danjulio/gCore-featherwing/pictures/gcore_assy_1.png

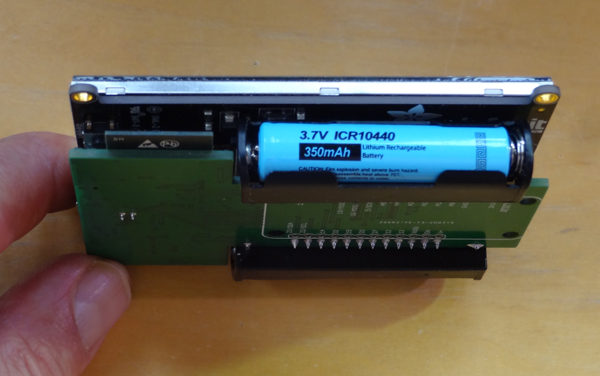
pictures/gcore_assy_1.png
