danjulio/gCore-featherwing/pictures/gcore_rev1_top.png

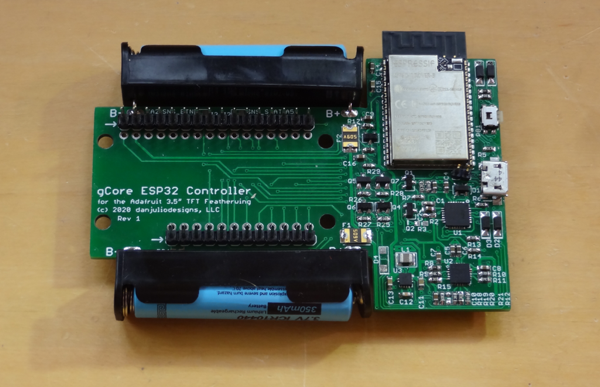
pictures/gcore_rev1_top.png
