danjulio/gCore-featherwing/pictures/gcore_side.png

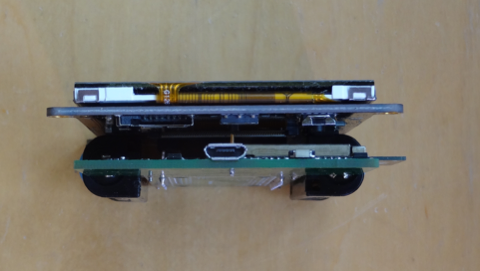
pictures/gcore_side.png
