danjulio/gCore-featherwing/software/LittlevGL/life/components/lvgl_esp32_drivers/lvgl_tft/disp_driver.c

/**
 * @file disp_driver.c
 */

#include "disp_driver.h"
#include "disp_spi.h"
#include "hx8357.h"


void disp_driver_init(bool init_spi)
{
	if (init_spi) {
		disp_spi_init();
	}
	
	hx8357_init(HX8357D);
}

void disp_driver_flush(lv_disp_drv_t * drv, const lv_area_t * area, lv_color_t * color_map)
{
	hx8357_flush(drv, area, color_map);
}
