danjulio/gCore-featherwing/software/FabGL/src/terminal.cpp

/*
  Created by Fabrizio Di Vittorio (fdivitto2013@gmail.com) - <http://www.fabgl.com>
  Copyright (c) 2019-2020 Fabrizio Di Vittorio.
  All rights reserved.

  This file is part of FabGL Library.

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
  You should have received a copy of the GNU General Public License
  along with FabGL.  If not, see <http://www.gnu.org/licenses/>.
 */


#include <stdarg.h>
#include <string.h>

#include "freertos/FreeRTOS.h"
#include "freertos/task.h"
#include "freertos/timers.h"

#include "rom/ets_sys.h"
#include "esp_attr.h"
#include "esp_intr.h"
#include "rom/uart.h"
#include "soc/uart_reg.h"
#include "soc/uart_struct.h"
#include "soc/io_mux_reg.h"
#include "soc/gpio_sig_map.h"
#include "soc/dport_reg.h"
#include "soc/rtc.h"
#include "esp_intr_alloc.h"


#include "fabutils.h"
#include "terminal.h"





namespace fabgl {


// Terminal identification ID
// 64 = VT420
// 1 = support for 132 columns
// 6 = selective erase
// 22 = color
const char TERMID[] = "?64;1;6;22c";

// to send 8 bit (S8C1T) or 7 bit control characters
const char CSI_7BIT[] = "\e[";
const char CSI_8BIT[] = "\x9B";
const char DCS_7BIT[] = "\eP";
const char DCS_8BIT[] = "\x90";
const char SS2_7BIT[] = "\eN";
const char SS2_8BIT[] = "\x8E";
const char SS3_7BIT[] = "\eO";
const char SS3_8BIT[] = "\x8F";
const char ST_7BIT[]  = "\e\\";
const char ST_8BIT[]  = "\x9C";
const char OSC_7BIT[] = "\e]";
const char OSC_8BIT[] = "\x9D";



#define ISCTRLCHAR(c) ((c) <= ASCII_US || (c) == ASCII_DEL)


// Map "DEC Special Graphics Character Set" to CP437
static const uint8_t DECGRAPH_TO_CP437[255] = {0, 1, 2, 3, 4, 5, 6, 7, 8, 9, 10, 11, 12, 13, 14, 15, 16, 17, 18, 19, 20, 21, 22, 23, 24, 25,
                                               26, 27, 28, 29, 30, 31, 32, 33, 34, 35, 36, 37, 38, 39, 40, 41, 42, 43, 44, 45, 46, 47, 48, 49,
                                               50, 51, 52, 53, 54, 55, 56, 57, 58, 59, 60, 61, 62, 63, 64, 65, 66, 67, 68, 69, 70, 71, 72, 73,
                                               74, 75, 76, 77, 78, 79, 80, 81, 82, 83, 84, 85, 86, 87, 88, 89, 90, 91, 92, 93, 94,
                                               /* 95 */ 32, /* 96 */ 4, /* 97 */ 177, /* 98 (not implemented) */ 63, /* 99 (not implemented) */ 63,
                                               /* 100 (not implemented) */ 63, /* 101 (not implemented) */ 63, /* 102 */ 248, /* 103 */ 241,
                                               /* 104 (not implemented) */ 63, /* 105 (not implemented) */ 63, /* 106 */ 217, /* 107 */ 191, /* 108 */ 218,
                                               /* 109 */ 192, /* 110 */ 197, /* 111 (not implemented) */ 63, /* 112 (not implemented) */ 63, /* 113 */ 196,
                                               /* 114 (not implemented) */ 63, /* 115 (not implemented) */ 63, /* 116 */ 195, /* 117 */ 180, /* 118 */ 193,
                                               /* 119 */ 194, /* 120 */ 179, /* 121 */ 243, /* 122 */ 242, /* 123 */ 227, /* 124 (not implemented) */ 63,
                                               /* 125 */ 156, /* 126 */ 249};


const char * CTRLCHAR_TO_STR[] = {"NUL", "SOH", "STX", "ETX", "EOT", "ENQ", "ACK", "BELL", "BS", "HT", "LF", "VT", "FF", "CR", "SO", "SI", "DLE", "XON", "DC2",
                                  "XOFF", "DC4", "NAK", "SYN", "ETB", "CAN", "EM", "SUB", "ESC", "FS", "GS", "RS", "US", "SPC"};



Terminal::Terminal()
  : m_canvas(nullptr)
{
}


Terminal::~Terminal()
{
  delete m_canvas;
}


void Terminal::begin(DisplayController * displayController, Keyboard * keyboard)
{
  m_displayController = displayController;

  m_canvas = new Canvas(m_displayController);

  m_keyboard = keyboard;
  if (m_keyboard == nullptr && PS2Controller::instance()) {
    // get default keyboard from PS/2 controller
    m_keyboard = PS2Controller::instance()->keyboard();
  }

  m_logStream = nullptr;

  m_glyphsBuffer = (GlyphsBuffer){0, 0, nullptr, 0, 0, nullptr};

  m_emuState.tabStop = nullptr;
  m_font.data = nullptr;

  set132ColumnMode(false);

  m_savedCursorStateList = nullptr;

  m_alternateScreenBuffer = false;
  m_alternateMap = nullptr;

  m_autoXONOFF = false;
  m_XOFF = false;

  // conformance level
  m_emuState.conformanceLevel = 4; // VT400
  m_emuState.ctrlBits = 7;

  // cursor setup
  m_cursorState   = false;
  m_emuState.cursorEnabled = false;

  m_mutex = xSemaphoreCreateMutex();

  // blink support
  m_blinkTimer = xTimerCreate("", pdMS_TO_TICKS(FABGLIB_DEFAULT_BLINK_PERIOD_MS), pdTRUE, this, blinkTimerFunc);
  xTimerStart(m_blinkTimer, portMAX_DELAY);

  // queue and task to consume input characters
  m_inputQueue = xQueueCreate(FABGLIB_TERMINAL_INPUT_QUEUE_SIZE, sizeof(uint8_t));
  xTaskCreate(&charsConsumerTask, "", FABGLIB_CHARS_CONSUMER_TASK_STACK_SIZE, this, FABGLIB_CHARS_CONSUMER_TASK_PRIORITY, &m_charsConsumerTaskHandle);

  m_defaultBackgroundColor = Color::Black;
  m_defaultForegroundColor = Color::White;

  m_serialPort = nullptr;
  m_keyboardReaderTaskHandle = nullptr;
  m_uart = false;

  m_outputQueue = nullptr;

  m_termInfo = nullptr;

  reset();
}


void Terminal::connectSerialPort(HardwareSerial & serialPort, bool autoXONXOFF)
{
  if (m_serialPort)
    vTaskDelete(m_keyboardReaderTaskHandle);
  m_serialPort = &serialPort;
  m_autoXONOFF = autoXONXOFF;

  m_serialPort->setRxBufferSize(FABGLIB_TERMINAL_INPUT_QUEUE_SIZE);

  if (m_keyboard->isKeyboardAvailable())
    xTaskCreate(&keyboardReaderTask, "", FABGLIB_KEYBOARD_READER_TASK_STACK_SIZE, this, FABGLIB_KEYBOARD_READER_TASK_PRIORITY, &m_keyboardReaderTaskHandle);

  // just in case a reset occurred after an XOFF
  if (m_autoXONOFF)
    send(ASCII_XON);
}


// returns number of bytes received (in the UART2 rx fifo buffer)
inline int uartGetRXFIFOCount()
{
  uart_dev_t * uart = (volatile uart_dev_t *)(DR_REG_UART2_BASE);
  return uart->status.rxfifo_cnt | ((int)(uart->mem_cnt_status.rx_cnt) << 8);
}


// flushes TX buffer of UART2
static void uartFlushTXFIFO()
{
  uart_dev_t * uart = (volatile uart_dev_t *)(DR_REG_UART2_BASE);
  while (uart->status.txfifo_cnt || uart->status.st_utx_out)
    ;
}


// flushes RX buffer of UART2
static void uartFlushRXFIFO()
{
  uart_dev_t * uart = (volatile uart_dev_t *)(DR_REG_UART2_BASE);
  while (uartGetRXFIFOCount() != 0 || uart->mem_rx_status.wr_addr != uart->mem_rx_status.rd_addr)
    uart->fifo.rw_byte;
}


// look into input queue (m_inputQueue): if there is space for new incoming bytes send XON and reenable uart RX interrupts
void Terminal::uartCheckInputQueueForFlowControl()
{
  if (m_autoXONOFF) {
    uart_dev_t * uart = (volatile uart_dev_t *)(DR_REG_UART2_BASE);
    if (uxQueueMessagesWaiting(m_inputQueue) == 0 && uart->int_ena.rxfifo_full == 0) {
      if (m_XOFF) {
        m_XOFF = false;
        uart->flow_conf.send_xon = 1; // send XON
      }
      uart->int_ena.rxfifo_full = 1;
    }
  }
}


// connect to UART2
void Terminal::connectSerialPort(uint32_t baud, uint32_t config, int rxPin, int txPin, FlowControl flowControl, bool inverted)
{
  Serial2.end();

  m_uart = true;
  m_autoXONOFF = (flowControl == FlowControl::Software);

  uart_dev_t * uart = (volatile uart_dev_t *)(DR_REG_UART2_BASE);

  DPORT_SET_PERI_REG_MASK(DPORT_PERIP_CLK_EN_REG, DPORT_UART2_CLK_EN);
  DPORT_CLEAR_PERI_REG_MASK(DPORT_PERIP_RST_EN_REG, DPORT_UART2_RST);

  // flush
  uartFlushTXFIFO();
  uartFlushRXFIFO();

  // set baud rate
  uint32_t clk_div = (getApbFrequency() << 4) / baud;
  uart->clk_div.div_int  = clk_div >> 4;
  uart->clk_div.div_frag = clk_div & 0xf;

  // frame
  uart->conf0.val = config;
  if (uart->conf0.stop_bit_num == 0x3) {
    uart->conf0.stop_bit_num = 1;
    uart->rs485_conf.dl1_en  = 1;
  }

  // RX Pin
  pinMode(rxPin, INPUT);
  pinMatrixInAttach(rxPin, U2RXD_IN_IDX, inverted);

  // RX interrupt
  uart->conf1.rxfifo_full_thrhd = 1;  // an interrupt for each character received
  uart->conf1.rx_tout_thrhd = 2;      // actually not used
  uart->conf1.rx_tout_en    = 0;      // timeout not enabled
  uart->int_ena.rxfifo_full = 1;      // interrupt on FIFO full (1 character - see rxfifo_full_thrhd)
  uart->int_ena.frm_err     = 1;      // interrupt on frame error
  uart->int_ena.rxfifo_tout = 0;      // no interrupt on rx timeout (see rx_tout_en and rx_tout_thrhd)
  uart->int_ena.parity_err  = 1;      // interrupt on rx parity error
  uart->int_ena.rxfifo_ovf  = 1;      // interrupt on rx overflow
  uart->int_clr.val = 0xffffffff;
  esp_intr_alloc(ETS_UART2_INTR_SOURCE, 0, uart_isr, this, nullptr);

  // setup FIFOs size
  uart->mem_conf.rx_size = 3;  // RX: 384 bytes (this is the max for UART2)
  uart->mem_conf.tx_size = 1;  // TX: 128 bytes

  // TX Pin
  pinMode(txPin, OUTPUT);
  pinMatrixOutAttach(txPin, U2TXD_OUT_IDX, inverted, false);

  // Flow Control
  uart->flow_conf.sw_flow_con_en = 0;
  uart->flow_conf.xonoff_del     = 0;
  if (flowControl == FlowControl::Software) {
    // we actually use manual software control, using send_xon/send_xoff bits to send control characters
    // because we have to check both RX-FIFO and input queue
    uart->swfc_conf.xon_threshold  = 0;
    uart->swfc_conf.xoff_threshold = 0;
    uart->swfc_conf.xon_char  = ASCII_XON;
    uart->swfc_conf.xoff_char = ASCII_XOFF;
    // send an XON right now
    m_XOFF = true;
    uart->flow_conf.send_xon = 1;
  }

  // APB Change callback (TODO?)
  //addApbChangeCallback(this, uart_on_apb_change);

  if (m_keyboard->isKeyboardAvailable())
    xTaskCreate(&keyboardReaderTask, "", FABGLIB_KEYBOARD_READER_TASK_STACK_SIZE, this, FABGLIB_KEYBOARD_READER_TASK_PRIORITY, &m_keyboardReaderTaskHandle);
}


void Terminal::connectLocally()
{
  m_outputQueue = xQueueCreate(FABGLIB_TERMINAL_OUTPUT_QUEUE_SIZE, sizeof(uint8_t));
  if (!m_keyboardReaderTaskHandle && m_keyboard->isKeyboardAvailable()) {
    xTaskCreate(&keyboardReaderTask, "", FABGLIB_KEYBOARD_READER_TASK_STACK_SIZE, this, FABGLIB_KEYBOARD_READER_TASK_PRIORITY, &m_keyboardReaderTaskHandle);
  }
}


void Terminal::logFmt(const char * format, ...)
{
  if (m_logStream) {
    va_list ap;
    va_start(ap, format);
    int size = vsnprintf(nullptr, 0, format, ap) + 1;
    if (size > 0) {
      char buf[size + 1];
      vsnprintf(buf, size, format, ap);
      m_logStream->write(buf);
    }
    va_end(ap);
  }
}


void Terminal::log(const char * txt)
{
  if (m_logStream)
    m_logStream->write(txt);
}


void Terminal::log(char c)
{
  if (m_logStream)
    m_logStream->write(c);
}


void Terminal::freeFont()
{
  #if FABGLIB_CACHE_FONT_IN_RAM
  if (m_font.data) {
    free((void*) m_font.data);
    m_font.data = nullptr;
  }
  #endif
}


void Terminal::freeTabStops()
{
  if (m_emuState.tabStop) {
    free(m_emuState.tabStop);
    m_emuState.tabStop = nullptr;
  }
}


void Terminal::freeGlyphsMap()
{
  if (m_glyphsBuffer.map) {
    free((void*) m_glyphsBuffer.map);
    m_glyphsBuffer.map = nullptr;
  }
  if (m_alternateMap) {
    free((void*) m_alternateMap);
    m_alternateMap = nullptr;
  }
}


void Terminal::end()
{
  vTaskDelete(m_keyboardReaderTaskHandle);

  xTimerDelete(m_blinkTimer, portMAX_DELAY);
  vSemaphoreDelete(m_mutex);

  clearSavedCursorStates();

  vTaskDelete(m_charsConsumerTaskHandle);
  vQueueDelete(m_inputQueue);

  vQueueDelete(m_outputQueue);

  freeFont();
  freeTabStops();
  freeGlyphsMap();
}


void Terminal::reset()
{
  #if FABGLIB_TERMINAL_DEBUG_REPORT_DESCS
  log("reset()\n");
  #endif

  xSemaphoreTake(m_mutex, portMAX_DELAY);
  m_resetRequested = false;

  m_emuState.originMode            = false;
  m_emuState.wraparound            = true;
  m_emuState.insertMode            = false;
  m_emuState.newLineMode           = false;
  m_emuState.smoothScroll          = false;
  m_emuState.keypadMode            = KeypadMode::Numeric;
  m_emuState.cursorKeysMode        = false;
  m_emuState.keyAutorepeat         = true;
  m_emuState.cursorBlinkingEnabled = true;
  m_emuState.cursorStyle           = 0;
  m_emuState.allow132ColumnMode    = false;
  m_emuState.reverseWraparoundMode = false;
  m_emuState.backarrowKeyMode      = false;
  m_emuState.ANSIMode              = true;
  m_emuState.VT52GraphicsMode      = false;
  m_emuState.allowFabGLSequences   = 0;
  m_emuState.characterSetIndex     = 0;  // Select G0
  for (int i = 0; i < 4; ++i)
    m_emuState.characterSet[i] = 1;     // G0, G1, G2 and G3 = USASCII

  m_lastPressedKey = VK_NONE;

  m_blinkingTextVisible = false;
  m_blinkingTextEnabled = true;

  m_cursorState = false;

  m_convMatchedCount = 0;
  m_convMatchedItem  = nullptr;

  // this also restore cursor at top-left
  setScrollingRegion(1, m_rows);

  resetTabStops();

  m_glyphOptions = (GlyphOptions) {{
    .fillBackground   = 1,
    .bold             = 0,
    .reduceLuminosity = 0,
    .italic           = 0,
    .invert           = 0,
    .blank            = 0,
    .underline        = 0,
    .doubleWidth      = 0,
    .userOpt1         = 0,    // blinking
    .userOpt2         = 0,    // 0 = erasable by DECSED or DECSEL,  1 = not erasable by DECSED or DECSEL
  }};
  m_canvas->setGlyphOptions(m_glyphOptions);

  m_paintOptions = PaintOptions();

  reverseVideo(false);

  int_setBackgroundColor(m_defaultBackgroundColor);
  int_setForegroundColor(m_defaultForegroundColor);

  clearSavedCursorStates();

  int_clear();

  xSemaphoreGive(m_mutex);
}


void Terminal::loadFont(FontInfo const * font)
{
  #if FABGLIB_TERMINAL_DEBUG_REPORT_DESCS
  log("loadFont()\n");
  #endif

  freeFont();

  m_font = *font;
#if FABGLIB_CACHE_FONT_IN_RAM
  int size = m_font.height * 256 * ((m_font.width + 7) / 8);
  m_font.data = (uint8_t const*) malloc(size);
  memcpy((void*)m_font.data, font->data, size);
#else
  m_font.data = font->data;
#endif

  m_columns = tmin(m_canvas->getWidth() / m_font.width, 132);
  m_rows    = tmin(m_canvas->getHeight() / m_font.height, 32);

  freeTabStops();
  m_emuState.tabStop = (uint8_t*) malloc(m_columns);
  resetTabStops();

  freeGlyphsMap();
  m_glyphsBuffer.glyphsWidth  = m_font.width;
  m_glyphsBuffer.glyphsHeight = m_font.height;
  m_glyphsBuffer.glyphsData   = m_font.data;
  m_glyphsBuffer.columns      = m_columns;
  m_glyphsBuffer.rows         = m_rows;
  m_glyphsBuffer.map          = (uint32_t*) heap_caps_malloc(sizeof(uint32_t) * m_columns * m_rows, MALLOC_CAP_32BIT);
  m_alternateMap = nullptr;
  m_alternateScreenBuffer = false;

  setScrollingRegion(1, m_rows);
}


void Terminal::flush(bool waitVSync)
{
  #if FABGLIB_TERMINAL_DEBUG_REPORT_DESCS
  log("flush()\n");
  #endif

  while (uxQueueMessagesWaiting(m_inputQueue) > 0)
    ;
  m_canvas->waitCompletion(waitVSync);
}


// false = setup for 80 columns mode
// true = setup for 132 columns mode
void Terminal::set132ColumnMode(bool value)
{
  #if FABGLIB_TERMINAL_DEBUG_REPORT_DESCS
  log("set132ColumnMode()\n");
  #endif

  loadFont(getPresetFontInfo(m_canvas->getWidth(), m_canvas->getHeight(), (value ? 132 : 80), 25));
}


void Terminal::setBackgroundColor(Color color, bool setAsDefault)
{
  if (setAsDefault)
    m_defaultBackgroundColor = color;
  Print::printf("\e[%dm", (int)color + (color < Color::BrightBlack ? 40 : 92));
}


void Terminal::int_setBackgroundColor(Color color)
{
  m_emuState.backgroundColor = color;
  m_canvas->setBrushColor(color);
}


void Terminal::setForegroundColor(Color color, bool setAsDefault)
{
  if (setAsDefault)
    m_defaultForegroundColor = color;
  Print::printf("\e[%dm", (int)color + (color < Color::BrightBlack ? 30 : 82));
}


void Terminal::int_setForegroundColor(Color color)
{
  m_emuState.foregroundColor = color;
  m_canvas->setPenColor(color);
}


void Terminal::reverseVideo(bool value)
{
  if (m_paintOptions.swapFGBG != value) {
    m_paintOptions.swapFGBG = value;
    m_canvas->setPaintOptions(m_paintOptions);

    m_canvas->swapRectangle(0, 0, m_canvas->getWidth() - 1, m_canvas->getHeight() - 1);
  }
}


void Terminal::clear(bool moveCursor)
{
  Print::write("\e[2J");
  if (moveCursor)
    Print::write("\e[1;1H");
}


void Terminal::int_clear()
{
  #if FABGLIB_TERMINAL_DEBUG_REPORT_DESCS
  log("int_clear()\n");
  #endif

  m_canvas->clear();
  clearMap(m_glyphsBuffer.map);
}


void Terminal::clearMap(uint32_t * map)
{
  uint32_t itemValue = GLYPHMAP_ITEM_MAKE(ASCII_SPC, m_emuState.backgroundColor, m_emuState.foregroundColor, m_glyphOptions);
  uint32_t * mapItemPtr = map;
  for (int row = 0; row < m_rows; ++row)
    for (int col = 0; col < m_columns; ++col, ++mapItemPtr)
      *mapItemPtr = itemValue;
}


// return True if scroll down required
bool Terminal::moveUp()
{
  #if FABGLIB_TERMINAL_DEBUG_REPORT_DESCS
  log("moveUp()\n");
  #endif

  if (m_emuState.cursorY == m_emuState.scrollingRegionTop)
    return true;
  setCursorPos(m_emuState.cursorX, m_emuState.cursorY - 1);
  return false;
}


// return True if scroll up required
bool Terminal::moveDown()
{
  #if FABGLIB_TERMINAL_DEBUG_REPORT_DESCS
  log("moveDown()\n");
  #endif

  if (m_emuState.cursorY == m_emuState.scrollingRegionDown)
    return true;
  setCursorPos(m_emuState.cursorX, m_emuState.cursorY + 1);
  return false;
}


// Move cursor at left or right, wrapping lines if necessary
void Terminal::move(int offset)
{
  int pos = m_emuState.cursorX - 1 + (m_emuState.cursorY - 1) * m_columns + offset;  // pos is zero based
  int newY = pos / m_columns + 1;
  int newX = pos % m_columns + 1;
  if (newY < m_emuState.scrollingRegionTop) {
    newX = 1;
    newY = m_emuState.scrollingRegionTop;
  }
  if (newY > m_emuState.scrollingRegionDown) {
    newX = m_columns;
    newY = m_emuState.scrollingRegionDown;
  }
  setCursorPos(newX, newY);
}


void Terminal::setCursorPos(int X, int Y)
{
  m_emuState.cursorX = tclamp(X, 1, (int)m_columns);
  m_emuState.cursorY = tclamp(Y, 1, (int)m_rows);
  m_emuState.cursorPastLastCol = false;

  #if FABGLIB_TERMINAL_DEBUG_REPORT_DESCSALL
  logFmt("setCursorPos(%d, %d) => set to (%d, %d)\n", X, Y, m_emuState.cursorX, m_emuState.cursorY);
  #endif
}


int Terminal::getAbsoluteRow(int Y)
{
  #if FABGLIB_TERMINAL_DEBUG_REPORT_DESCS
  logFmt("getAbsoluteRow(%d)\n", Y);
  #endif

  if (m_emuState.originMode) {
    Y += m_emuState.scrollingRegionTop - 1;
    Y = tclamp(Y, m_emuState.scrollingRegionTop, m_emuState.scrollingRegionDown);
  }
  return Y;
}


void Terminal::enableCursor(bool value)
{
  Print::write("\e[?25");
  Print::write(value ? "h" : "l");
}


bool Terminal::int_enableCursor(bool value)
{
  bool prev = m_emuState.cursorEnabled;
  if (m_emuState.cursorEnabled != value) {
    m_emuState.cursorEnabled = value;
    if (m_emuState.cursorEnabled) {
      if (uxQueueMessagesWaiting(m_inputQueue) == 0)
        blinkCursor();  // just to show the cursor immediately
    } else {
      if (m_cursorState)
        blinkCursor(); // make sure cursor is hidden
    }
  }
  return prev;
}


bool Terminal::enableBlinkingText(bool value)
{
  bool prev = m_blinkingTextEnabled;
  m_blinkingTextEnabled = value;
  return prev;
}


// callback for blink timer
void Terminal::blinkTimerFunc(TimerHandle_t xTimer)
{
  Terminal * term = (Terminal*) pvTimerGetTimerID(xTimer);

  if (xSemaphoreTake(term->m_mutex, 0) == pdTRUE) {

    // cursor blink
    if (term->m_emuState.cursorEnabled && term->m_emuState.cursorBlinkingEnabled)
      term->blinkCursor();

    // text blink
    if (term->m_blinkingTextEnabled)
      term->blinkText();

    xSemaphoreGive(term->m_mutex);

  }
}


void Terminal::blinkCursor()
{
  m_cursorState = !m_cursorState;
  int X = (m_emuState.cursorX - 1) * m_font.width;
  int Y = (m_emuState.cursorY - 1) * m_font.height;
  switch (m_emuState.cursorStyle) {
    case 0 ... 2:
      // block cursor
      m_canvas->swapRectangle(X, Y, X + m_font.width - 1, Y + m_font.height - 1);
      break;
    case 3 ... 4:
      // underline cursor
      m_canvas->swapRectangle(X, Y + m_font.height - 2, X + m_font.width - 1, Y + m_font.height - 1);
      break;
    case 5 ... 6:
      // bar cursor
      m_canvas->swapRectangle(X, Y, X + 1, Y + m_font.height - 1);
      break;
  }
}


void Terminal::blinkText()
{
  m_blinkingTextVisible = !m_blinkingTextVisible;
  bool keepEnabled = false;
  int rows = m_rows;
  int cols = m_columns;
  m_canvas->beginUpdate();
  for (int y = 0; y < rows; ++y) {
    uint32_t * itemPtr = m_glyphsBuffer.map + y * cols;
    for (int x = 0; x < cols; ++x, ++itemPtr) {
      // character to blink?
      GlyphOptions glyphOptions = glyphMapItem_getOptions(itemPtr);
      if (glyphOptions.userOpt1) {
        glyphOptions.blank = !m_blinkingTextVisible;
        glyphMapItem_setOptions(itemPtr, glyphOptions);
        refresh(x + 1, y + 1);
        keepEnabled = true;
      }
    }
    m_canvas->waitCompletion(false);
  }
  m_canvas->endUpdate();
  if (!keepEnabled)
    m_blinkingTextEnabled = false;
}


void Terminal::nextTabStop()
{
  int actualColumns = m_columns;

  // if double width for current line then consider half columns
  if (getGlyphOptionsAt(1, m_emuState.cursorY).doubleWidth)
    actualColumns /= 2;

  int x = m_emuState.cursorX;
  while (x < actualColumns) {
    ++x;
    if (m_emuState.tabStop[x - 1])
      break;
  }
  setCursorPos(x, m_emuState.cursorY);
}


// setup tab stops. One every 8.
void Terminal::resetTabStops()
{
  for (int i = 0; i < m_columns; ++i)
    m_emuState.tabStop[i] = (i > 0 && (i % 8) == 0 ? 1 : 0);
}


// if column = 0 then clear all tab stops
void Terminal::setTabStop(int column, bool set)
{
  #if FABGLIB_TERMINAL_DEBUG_REPORT_DESCS
  logFmt("setTabStop %d %d\n", column, (int)set);
  #endif

  if (column == 0)
    memset(m_emuState.tabStop, 0, m_columns);
  else
    m_emuState.tabStop[column - 1] = set ? 1 : 0;
}


void Terminal::scrollDown()
{
  #if FABGLIB_TERMINAL_DEBUG_REPORT_DESCS
  log("scrollDown\n");
  #endif

  // scroll down using canvas
  if (m_emuState.smoothScroll) {
    for (int i = 0; i < m_font.height; ++i)
      m_canvas->scroll(0, 1);
  } else
    m_canvas->scroll(0, m_font.height);

  // move down scren buffer
  for (int y = m_emuState.scrollingRegionDown - 1; y > m_emuState.scrollingRegionTop - 1; --y)
    memcpy(m_glyphsBuffer.map + y * m_columns, m_glyphsBuffer.map + (y - 1) * m_columns, m_columns * sizeof(uint32_t));

  // insert a blank line in the screen buffer
  uint32_t itemValue = GLYPHMAP_ITEM_MAKE(ASCII_SPC, m_emuState.backgroundColor, m_emuState.foregroundColor, m_glyphOptions);
  uint32_t * itemPtr = m_glyphsBuffer.map + (m_emuState.scrollingRegionTop - 1) * m_columns;
  for (int x = 0; x < m_columns; ++x, ++itemPtr)
    *itemPtr = itemValue;

}


// startingRow: represents an absolute value, not related to the scrolling region
void Terminal::scrollDownAt(int startingRow)
{
  int prevScrollingRegionTop = m_emuState.scrollingRegionTop;
  setScrollingRegion(startingRow, m_emuState.scrollingRegionDown, false);

  scrollDown();

  setScrollingRegion(prevScrollingRegionTop, m_emuState.scrollingRegionDown, false);
}


void Terminal::scrollUp()
{
  #if FABGLIB_TERMINAL_DEBUG_REPORT_DESCS
  log("scrollUp\n");
  #endif

  // scroll up using canvas
  if (m_emuState.smoothScroll) {
    for (int i = 0; i < m_font.height; ++i)
      m_canvas->scroll(0, -1);
  } else
    m_canvas->scroll(0, -m_font.height);

  // move up screen buffer
  for (int y = m_emuState.scrollingRegionTop - 1; y < m_emuState.scrollingRegionDown - 1; ++y)
    memcpy(m_glyphsBuffer.map + y * m_columns, m_glyphsBuffer.map + (y + 1) * m_columns, m_columns * sizeof(uint32_t));

  // insert a blank line in the screen buffer
  uint32_t itemValue = GLYPHMAP_ITEM_MAKE(ASCII_SPC, m_emuState.backgroundColor, m_emuState.foregroundColor, m_glyphOptions);
  uint32_t * itemPtr = m_glyphsBuffer.map + (m_emuState.scrollingRegionDown - 1) * m_columns;
  for (int x = 0; x < m_columns; ++x, ++itemPtr)
    *itemPtr = itemValue;
}


void Terminal::scrollUpAt(int startingRow)
{
  int prevScrollingRegionTop = m_emuState.scrollingRegionTop;
  setScrollingRegion(startingRow, m_emuState.scrollingRegionDown, false);

  scrollUp();

  setScrollingRegion(prevScrollingRegionTop, m_emuState.scrollingRegionDown, false);
}


void Terminal::setScrollingRegion(int top, int down, bool resetCursorPos)
{
  m_emuState.scrollingRegionTop  = tclamp(top, 1, (int)m_rows);
  m_emuState.scrollingRegionDown = tclamp(down, 1, (int)m_rows);
  updateCanvasScrollingRegion();

  if (resetCursorPos)
    setCursorPos(1, m_emuState.originMode ? m_emuState.scrollingRegionTop : 1);

  #if FABGLIB_TERMINAL_DEBUG_REPORT_DESCS
  logFmt("setScrollingRegion: %d %d => %d %d\n", top, down, m_emuState.scrollingRegionTop, m_emuState.scrollingRegionDown);
  #endif
}


void Terminal::updateCanvasScrollingRegion()
{
  m_canvas->setScrollingRegion(0, (m_emuState.scrollingRegionTop - 1) * m_font.height, m_canvas->getWidth() - 1, m_emuState.scrollingRegionDown * m_font.height - 1);
}


// Insert a blank space at current position, moving next "charsToMove" characters to the right (even on multiple lines).
// Characters after "charsToMove" length are overwritter.
// Vertical scroll may occurs (in this case returns "True")
bool Terminal::multilineInsertChar(int charsToMove)
{
  bool scrolled = false;
  int col = m_emuState.cursorX;
  int row = m_emuState.cursorY;
  if (m_emuState.cursorPastLastCol) {
    ++row;
    col = 1;
  }
  uint32_t lastColItem = 0;
  while (charsToMove > 0) {
    uint32_t * rowPtr = m_glyphsBuffer.map + (row - 1) * m_columns;
    uint32_t lItem = rowPtr[m_columns - 1];
    insertAt(col, row, 1);
    if (row > m_emuState.cursorY) {
      rowPtr[0] = lastColItem;
      refresh(1, row);
    }
    lastColItem = lItem;
    charsToMove -= m_columns - col;
    col = 1;
    if (charsToMove > 0 && row == m_emuState.scrollingRegionDown) {
      scrolled = true;
      scrollUp();
      setCursorPos(m_emuState.cursorX, m_emuState.cursorY - 1);
    } else {
      ++row;
    }
    m_canvas->waitCompletion(false);
  }
  return scrolled;
}


// inserts specified number of blank spaces at the specified row and column. Characters moved past the right border are lost.
void Terminal::insertAt(int column, int row, int count)
{
  #if FABGLIB_TERMINAL_DEBUG_REPORT_DESCS
  logFmt("insertAt(%d, %d, %d)\n", column, row, count);
  #endif

  count = tmin((int)m_columns, count);

  // move characters on the right using canvas
  int charWidth = getCharWidthAt(row);
  m_canvas->setScrollingRegion((column - 1) * charWidth, (row - 1) * m_font.height, charWidth * getColumnsAt(row) - 1, row * m_font.height - 1);
  m_canvas->scroll(count * charWidth, 0);
  updateCanvasScrollingRegion();  // restore original scrolling region

  // move characters in the screen buffer
  uint32_t * rowPtr = m_glyphsBuffer.map + (row - 1) * m_columns;
  for (int i = m_columns - 1; i >= column + count - 1; --i)
    rowPtr[i] = rowPtr[i - count];

  // fill blank characters
  GlyphOptions glyphOptions = m_glyphOptions;
  glyphOptions.doubleWidth = glyphMapItem_getOptions(rowPtr).doubleWidth;
  uint32_t itemValue = GLYPHMAP_ITEM_MAKE(ASCII_SPC, m_emuState.backgroundColor, m_emuState.foregroundColor, glyphOptions);
  for (int i = 0; i < count; ++i)
    rowPtr[column + i - 1] = itemValue;
}


void Terminal::multilineDeleteChar(int charsToMove)
{
  int col = m_emuState.cursorX;
  int row = m_emuState.cursorY;
  if (m_emuState.cursorPastLastCol) {
    ++row;
    col = 1;
  }

  // at least one char must be deleted
  if (charsToMove == 0)
    deleteAt(col, row, 1);

  while (charsToMove > 0) {
    deleteAt(col, row, 1);
    charsToMove -= m_columns - col;
    if (charsToMove > 0) {
      m_canvas->waitCompletion(false);
      uint32_t * lastItem  = m_glyphsBuffer.map + (row - 1) * m_columns + (m_columns - 1);
      lastItem[0] = lastItem[1];
      refresh(m_columns, row);
    }
    col = 1;
    ++row;
    m_canvas->waitCompletion(false);
  }
}


// deletes "count" characters from specified "row", starting from "column", scrolling left remaining characters
void Terminal::deleteAt(int column, int row, int count)
{
  #if FABGLIB_TERMINAL_DEBUG_REPORT_DESCS
  logFmt("deleteAt(%d, %d, %d)\n", column, row, count);
  #endif

  count = imin(m_columns - column + 1, count);

  // move characters on the right using canvas
  int charWidth = getCharWidthAt(row);
  m_canvas->setScrollingRegion((column - 1) * charWidth, (row - 1) * m_font.height, charWidth * getColumnsAt(row) - 1, row * m_font.height - 1);
  m_canvas->scroll(-count * charWidth, 0);
  updateCanvasScrollingRegion();  // restore original scrolling region

  // move characters in the screen buffer
  uint32_t * rowPtr = m_glyphsBuffer.map + (row - 1) * m_columns;
  int itemsToMove = m_columns - column - count + 1;
  for (int i = 0; i < itemsToMove; ++i)
    rowPtr[column - 1 + i] = rowPtr[column - 1 + i + count];

  // fill blank characters
  GlyphOptions glyphOptions = m_glyphOptions;
  glyphOptions.doubleWidth = glyphMapItem_getOptions(rowPtr).doubleWidth;
  uint32_t itemValue = GLYPHMAP_ITEM_MAKE(ASCII_SPC, m_emuState.backgroundColor, m_emuState.foregroundColor, glyphOptions);
  for (int i = m_columns - count + 1 ; i <= m_columns; ++i)
    rowPtr[i - 1] = itemValue;
}


// Coordinates are cursor coordinates (1,1  = top left)
// maintainDoubleWidth = true: Maintains line attributes (double width)
// selective = true: erase only characters with userOpt1 = 0
void Terminal::erase(int X1, int Y1, int X2, int Y2, char c, bool maintainDoubleWidth, bool selective)
{
  #if FABGLIB_TERMINAL_DEBUG_REPORT_DESCS
  logFmt("erase(%d, %d, %d, %d, %d, %d)\n", X1, Y1, X2, Y2, (int)c, (int)maintainDoubleWidth);
  #endif

  X1 = tclamp(X1 - 1, 0, (int)m_columns - 1);
  Y1 = tclamp(Y1 - 1, 0, (int)m_rows - 1);
  X2 = tclamp(X2 - 1, 0, (int)m_columns - 1);
  Y2 = tclamp(Y2 - 1, 0, (int)m_rows - 1);

  if (c == ASCII_SPC && !selective) {
    int charWidth = getCharWidthAt(m_emuState.cursorY);
    m_canvas->fillRectangle(X1 * charWidth, Y1 * m_font.height, (X2 + 1) * charWidth - 1, (Y2 + 1) * m_font.height - 1);
  }

  GlyphOptions glyphOptions = {.value = 0};
  glyphOptions.fillBackground = 1;

  for (int y = Y1; y <= Y2; ++y) {
    uint32_t * itemPtr = m_glyphsBuffer.map + X1 + y * m_columns;
    for (int x = X1; x <= X2; ++x, ++itemPtr) {
      if (selective && glyphMapItem_getOptions(itemPtr).userOpt2)  // bypass if protected item
        continue;
      glyphOptions.doubleWidth = maintainDoubleWidth ? glyphMapItem_getOptions(itemPtr).doubleWidth : 0;
      *itemPtr = GLYPHMAP_ITEM_MAKE(c, m_emuState.backgroundColor, m_emuState.foregroundColor, glyphOptions);
    }
  }
  if (c != ASCII_SPC || selective)
    refresh(X1 + 1, Y1 + 1, X2 + 1, Y2 + 1);
}


void Terminal::clearSavedCursorStates()
{
  #if FABGLIB_TERMINAL_DEBUG_REPORT_DESCS
  log("clearSavedCursorStates()\n");
  #endif

  for (TerminalCursorState * curItem = m_savedCursorStateList, * next; curItem; curItem = next) {
    next = curItem->next;
    free(curItem->tabStop);
    free(curItem);
  }
  m_savedCursorStateList = nullptr;
}


void Terminal::saveCursorState()
{
  #if FABGLIB_TERMINAL_DEBUG_REPORT_DESCS
  log("saveCursorState()\n");
  #endif

  TerminalCursorState * s = (TerminalCursorState*) malloc(sizeof(TerminalCursorState));

  if (s) {
    *s = (TerminalCursorState) {
      .next              = m_savedCursorStateList,
      .cursorX           = (int16_t) m_emuState.cursorX,
      .cursorY           = (int16_t) m_emuState.cursorY,
      .tabStop           = (uint8_t*) malloc(m_columns),
      .cursorPastLastCol = m_emuState.cursorPastLastCol,
      .originMode        = m_emuState.originMode,
      .glyphOptions      = m_glyphOptions,
      .characterSetIndex = m_emuState.characterSetIndex,
      .characterSet      = {m_emuState.characterSet[0], m_emuState.characterSet[1], m_emuState.characterSet[2], m_emuState.characterSet[3]},
    };
    if (s->tabStop)
      memcpy(s->tabStop, m_emuState.tabStop, m_columns);
    m_savedCursorStateList = s;
  } else {
    #if FABGLIB_TERMINAL_DEBUG_REPORT_ERRORS
    log("ERROR: Unable to alloc TerminalCursorState\n");
    #endif
  }
}


void Terminal::restoreCursorState()
{
  #if FABGLIB_TERMINAL_DEBUG_REPORT_DESCS
  log("restoreCursorState()\n");
  #endif

  if (m_savedCursorStateList) {
    m_emuState.cursorX = m_savedCursorStateList->cursorX;
    m_emuState.cursorY = m_savedCursorStateList->cursorY;
    m_emuState.cursorPastLastCol = m_savedCursorStateList->cursorPastLastCol;
    m_emuState.originMode = m_savedCursorStateList->originMode;
    if (m_savedCursorStateList->tabStop)
      memcpy(m_emuState.tabStop, m_savedCursorStateList->tabStop, m_columns);
    m_glyphOptions = m_savedCursorStateList->glyphOptions;
    m_canvas->setGlyphOptions(m_glyphOptions);
    m_emuState.characterSetIndex = m_savedCursorStateList->characterSetIndex;
    for (int i = 0; i < 4; ++i)
      m_emuState.characterSet[i] = m_savedCursorStateList->characterSet[i];

    TerminalCursorState * next = m_savedCursorStateList->next;

    free(m_savedCursorStateList->tabStop);
    free(m_savedCursorStateList);
    m_savedCursorStateList = next;
  }
}


void Terminal::useAlternateScreenBuffer(bool value)
{
  if (m_alternateScreenBuffer != value) {
    m_alternateScreenBuffer = value;
    if (!m_alternateMap) {
      // first usage, need to setup the alternate screen
      m_alternateMap = (uint32_t*) heap_caps_malloc(sizeof(uint32_t) * m_columns * m_rows, MALLOC_CAP_32BIT);
      clearMap(m_alternateMap);
      m_alternateCursorX = 1;
      m_alternateCursorY = 1;
    }
    tswap(m_alternateMap, m_glyphsBuffer.map);
    tswap(m_emuState.cursorX, m_alternateCursorX);
    tswap(m_emuState.cursorY, m_alternateCursorY);
    m_emuState.cursorPastLastCol = false;
    refresh();
  }
}


void Terminal::localInsert(uint8_t c)
{
  if (m_outputQueue)
    xQueueSendToFront(m_outputQueue, &c, portMAX_DELAY);
}


void Terminal::localWrite(uint8_t c)
{
  if (m_outputQueue)
    xQueueSendToBack(m_outputQueue, &c, portMAX_DELAY);
}


void Terminal::localWrite(char const * str)
{
  if (m_outputQueue) {
    while (*str) {
      xQueueSendToBack(m_outputQueue, str, portMAX_DELAY);

      #if FABGLIB_TERMINAL_DEBUG_REPORT_OUT_CODES
      logFmt("=> %02X  %s%c\n", (int)*str, (*str <= ASCII_SPC ? CTRLCHAR_TO_STR[(int)(*str)] : ""), (*str > ASCII_SPC ? *str : ASCII_SPC));
      #endif

      ++str;
    }
  }
}


int Terminal::available()
{
  return m_outputQueue ? uxQueueMessagesWaiting(m_outputQueue) : 0;
}


int Terminal::read()
{
  return read(-1);
}


int Terminal::read(int timeOutMS)
{
  if (m_outputQueue) {
    char c;
    xQueueReceive(m_outputQueue, &c, msToTicks(timeOutMS));
    return c;
  } else
    return -1;
}


bool Terminal::waitFor(int value, int timeOutMS)
{
  TimeOut timeout;
  while (!timeout.expired(timeOutMS)) {
    int c = read(timeOutMS);
    if (c == value)
      return true;
  }
  return false;
}


// not implemented
int Terminal::peek()
{
  return -1;
}


void Terminal::flush()
{
  flush(true);
}


void Terminal::pollSerialPort()
{
  while (true) {
    int avail = m_serialPort->available();

    if (m_autoXONOFF) {
      if (m_XOFF) {
        // XOFF already sent, need to send XON?
        if (avail < FABGLIB_TERMINAL_XON_THRESHOLD) {
          send(ASCII_XON);
          m_XOFF = false;
        }
      } else {
        // XOFF not sent, need to send XOFF?
        if (avail >= FABGLIB_TERMINAL_XOFF_THRESHOLD) {
          send(ASCII_XOFF);
          m_XOFF = true;
        }
      }
    }

    if (!avail)
      break;

    write( m_serialPort->read() );
  }
}


void IRAM_ATTR Terminal::uart_isr(void *arg)
{
  Terminal * term = (Terminal*) arg;
  uart_dev_t * uart = (volatile uart_dev_t *)(DR_REG_UART2_BASE);

  // look for overflow or RX errors
  if (uart->int_st.rxfifo_ovf || uart->int_st.frm_err || uart->int_st.parity_err) {
    // reset RX-FIFO, because hardware bug rxfifo_rst cannot be used, so just flush
    uartFlushRXFIFO();
    // reset interrupt flags
    uart->int_clr.rxfifo_ovf = 1;
    uart->int_clr.frm_err    = 1;
    uart->int_clr.parity_err = 1;
    return;
  }

  // software flow control?
  if (term->m_autoXONOFF) {
    // send XOFF/XON looking at RX FIFO occupation
    int count = uartGetRXFIFOCount();
    if (count > 300 && !term->m_XOFF) {
      uart->flow_conf.send_xoff = 1; // send XOFF
      term->m_XOFF = true;
    } else if (count < 20 && term->m_XOFF) {
      uart->flow_conf.send_xon = 1;  // send XON
      term->m_XOFF = false;
    }
  }

  // main receive loop
  while (uartGetRXFIFOCount() != 0 || uart->mem_rx_status.wr_addr != uart->mem_rx_status.rd_addr) {
    // look for enough room in input queue
    if (term->m_autoXONOFF && xQueueIsQueueFullFromISR(term->m_inputQueue)) {
      if (!term->m_XOFF) {
        uart->flow_conf.send_xoff = 1;  // send XOFF
        term->m_XOFF = true;
      }
      // block further interrupts
      uart->int_ena.rxfifo_full = 0;
      break;
    }
    // add to input queue
    term->addToInputQueue(uart->fifo.rw_byte, true);
  }

  // clear interrupt flag
  uart->int_clr.rxfifo_full = 1;
}


// send a character to m_serialPort or m_outputQueue
void Terminal::send(char c)
{
  #if FABGLIB_TERMINAL_DEBUG_REPORT_OUT_CODES
  logFmt("=> %02X  %s%c\n", (int)c, (c <= ASCII_SPC ? CTRLCHAR_TO_STR[(int)c] : ""), (c > ASCII_SPC ? c : ASCII_SPC));
  #endif

  if (m_serialPort) {
    while (m_serialPort->availableForWrite() == 0)
      vTaskDelay(1 / portTICK_PERIOD_MS);
    m_serialPort->write(c);
  }

  if (m_uart) {
    uart_dev_t * uart = (volatile uart_dev_t *)(DR_REG_UART2_BASE);
    while (uart->status.txfifo_cnt == 0x7F)
      ;
    uart->fifo.rw_byte = c;
  }

  localWrite(c);  // write to m_outputQueue
}


// send a string to m_serialPort or m_outputQueue
void Terminal::send(char const * str)
{
  if (m_serialPort) {
    while (*str) {
      while (m_serialPort->availableForWrite() == 0)
        vTaskDelay(1 / portTICK_PERIOD_MS);
      m_serialPort->write(*str);

      #if FABGLIB_TERMINAL_DEBUG_REPORT_OUT_CODES
      logFmt("=> %02X  %s%c\n", (int)*str, (*str <= ASCII_SPC ? CTRLCHAR_TO_STR[(int)(*str)] : ""), (*str > ASCII_SPC ? *str : ASCII_SPC));
      #endif

      ++str;
    }
  }

  if (m_uart) {
    uart_dev_t * uart = (volatile uart_dev_t *)(DR_REG_UART2_BASE);
    while (*str) {
      while (uart->status.txfifo_cnt == 0x7F)
        ;
      uart->fifo.rw_byte = *str++;
    }
  }

  localWrite(str);  // write to m_outputQueue
}


void Terminal::sendCSI()
{
  send(m_emuState.ctrlBits == 7 ? CSI_7BIT : CSI_8BIT);
}


void Terminal::sendDCS()
{
  send(m_emuState.ctrlBits == 7 ? DCS_7BIT : DCS_8BIT);
}


void Terminal::sendSS3()
{
  send(m_emuState.ctrlBits == 7 ? SS3_7BIT : SS3_8BIT);
}


int Terminal::availableForWrite()
{
  return uxQueueSpacesAvailable(m_inputQueue);
}


bool Terminal::addToInputQueue(char c, bool fromISR)
{
  if (fromISR)
    return xQueueSendToBackFromISR(m_inputQueue, &c, nullptr);
  else
    return xQueueSendToBack(m_inputQueue, &c, portMAX_DELAY);
}


void Terminal::write(char c, bool fromISR)
{
  if (m_termInfo == nullptr)
    addToInputQueue(c, fromISR);  // send unprocessed
  else
    convHandleTranslation(c, fromISR);

  #if FABGLIB_TERMINAL_DEBUG_REPORT_IN_CODES
  logFmt("<= %02X  %s%c\n", (int)c, (c <= ASCII_SPC ? CTRLCHAR_TO_STR[(int)c] : ""), (c > ASCII_SPC ? c : ASCII_SPC));
  #endif
}


size_t Terminal::write(uint8_t c)
{
  write(c, false);
  return 1;
}


int Terminal::write(const uint8_t * buffer, int size)
{
  for (int i = 0; i < size; ++i)
    write(*(buffer++));
  return size;
}


void Terminal::setTerminalType(TermInfo const * value)
{
  m_termInfo = nullptr;
  write("\e[?2h");  // disable VT52 mode
  if (value != nullptr)
    write(value->initString);
  m_termInfo = value;
}


void Terminal::setTerminalType(TermType value)
{
  switch (value) {
    case TermType::ANSI_VT:
      setTerminalType(nullptr);
      break;
    case TermType::ADM3A:
      setTerminalType(&term_ADM3A);
      break;
    case TermType::ADM31:
      setTerminalType(&term_ADM31);
      break;
    case TermType::Hazeltine1500:
      setTerminalType(&term_Hazeltine1500);
      break;
    case TermType::Osborne:
      setTerminalType(&term_Osborne);
      break;
    case TermType::Kaypro:
      setTerminalType(&term_Kaypro);
      break;
    case TermType::VT52:
      setTerminalType(&term_VT52);
      break;
  }
}


void Terminal::convHandleTranslation(uint8_t c, bool fromISR)
{
  if (m_convMatchedCount > 0 || c < 32 || c == 0x7f || c == '~') {

    m_convMatchedChars[m_convMatchedCount] = c;

    if (m_convMatchedItem == nullptr)
      m_convMatchedItem = m_termInfo->videoCtrlSet;

    for (auto item = m_convMatchedItem; item->termSeq; ++item) {
      if (item != m_convMatchedItem) {
        // check if this item can be a new candidate
        if (m_convMatchedCount == 0 || (item->termSeqLen > m_convMatchedCount && strncmp(item->termSeq, m_convMatchedItem->termSeq, m_convMatchedCount) == 0))
          m_convMatchedItem = item;
        else
          continue;
      }
      // here (item == m_convMatchedItem) is always true
      if (item->termSeq[m_convMatchedCount] == 0xFF || item->termSeq[m_convMatchedCount] == c) {
        // are there other chars to process?
        ++m_convMatchedCount;
        if (item->termSeqLen == m_convMatchedCount) {
          // full match, send related ANSI sequences (and resets m_convMatchedCount and m_convMatchedItem)
          for (ConvCtrl const * ctrl = item->convCtrl; *ctrl != ConvCtrl::END; ++ctrl)
            convSendCtrl(*ctrl, fromISR);
        }
        return;
      }
    }

    // no match, send received stuff as is
    convQueue(nullptr, fromISR);
  } else
    addToInputQueue(c, fromISR);
}


void Terminal::convSendCtrl(ConvCtrl ctrl, bool fromISR)
{
  switch (ctrl) {
    case ConvCtrl::CarriageReturn:
      convQueue("\x0d", fromISR);
      break;
    case ConvCtrl::LineFeed:
      convQueue("\x0a", fromISR);
      break;
    case ConvCtrl::CursorLeft:
      convQueue("\e[D", fromISR);
      break;
    case ConvCtrl::CursorUp:
      convQueue("\e[A", fromISR);
      break;
    case ConvCtrl::CursorRight:
      convQueue("\e[C", fromISR);
      break;
    case ConvCtrl::EraseToEndOfScreen:
      convQueue("\e[J", fromISR);
      break;
    case ConvCtrl::EraseToEndOfLine:
      convQueue("\e[K", fromISR);
      break;
    case ConvCtrl::CursorHome:
      convQueue("\e[H", fromISR);
      break;
    case ConvCtrl::AttrNormal:
      convQueue("\e[0m", fromISR);
      break;
    case ConvCtrl::AttrBlank:
      convQueue("\e[8m", fromISR);
      break;
    case ConvCtrl::AttrBlink:
      convQueue("\e[5m", fromISR);
      break;
    case ConvCtrl::AttrBlinkOff:
      convQueue("\e[25m", fromISR);
      break;
    case ConvCtrl::AttrReverse:
      convQueue("\e[7m", fromISR);
      break;
    case ConvCtrl::AttrReverseOff:
      convQueue("\e[27m", fromISR);
      break;
    case ConvCtrl::AttrUnderline:
      convQueue("\e[4m", fromISR);
      break;
    case ConvCtrl::AttrUnderlineOff:
      convQueue("\e[24m", fromISR);
      break;
    case ConvCtrl::AttrReduce:
      convQueue("\e[2m", fromISR);
      break;
    case ConvCtrl::AttrReduceOff:
      convQueue("\e[22m", fromISR);
      break;
    case ConvCtrl::InsertLine:
      convQueue("\e[L", fromISR);
      break;
    case ConvCtrl::InsertChar:
      convQueue("\e[@", fromISR);
      break;
    case ConvCtrl::DeleteLine:
      convQueue("\e[M", fromISR);
      break;
    case ConvCtrl::DeleteCharacter:
      convQueue("\e[P", fromISR);
      break;
    case ConvCtrl::CursorOn:
      convQueue("\e[?25h", fromISR);
      break;
    case ConvCtrl::CursorOff:
      convQueue("\e[?25l", fromISR);
      break;
    case ConvCtrl::SaveCursor:
      convQueue("\e[?1048h", fromISR);
      break;
    case ConvCtrl::RestoreCursor:
      convQueue("\e[?1048l", fromISR);
      break;
    case ConvCtrl::CursorPos:
    case ConvCtrl::CursorPos2:
    {
      char s[11];
      int y = (ctrl == ConvCtrl::CursorPos ? m_convMatchedChars[2] - 31 : m_convMatchedChars[3] + 1);
      int x = (ctrl == ConvCtrl::CursorPos ? m_convMatchedChars[3] - 31 : m_convMatchedChars[2] + 1);
      sprintf(s, "\e[%d;%dH", y, x);
      convQueue(s, fromISR);
      break;
    }

    default:
      break;
  }
}


// queue m_termMatchedChars[] or specified string
void Terminal::convQueue(const char * str, bool fromISR)
{
  if (str) {
    for (; *str; ++str)
      addToInputQueue(*str, fromISR);
  } else {
    for (int i = 0; i <= m_convMatchedCount; ++i) {
      addToInputQueue(m_convMatchedChars[i], fromISR);
    }
  }
  m_convMatchedCount = 0;
  m_convMatchedItem = nullptr;
}


// set specified character at current cursor position
// return true if vertical scroll happened
bool Terminal::setChar(char c)
{
  bool vscroll = false;

  if (m_emuState.cursorPastLastCol) {
    if (m_emuState.wraparound) {
      setCursorPos(1, m_emuState.cursorY); // this sets m_emuState.cursorPastLastCol = false
      if (moveDown()) {
        scrollUp();
        vscroll = true;
      }
    }
  }

  if (m_emuState.insertMode)
    insertAt(m_emuState.cursorX, m_emuState.cursorY, 1);

  GlyphOptions glyphOptions = m_glyphOptions;

  // doubleWidth must be maintained
  uint32_t * mapItemPtr = m_glyphsBuffer.map + (m_emuState.cursorX - 1) + (m_emuState.cursorY - 1) * m_columns;
  glyphOptions.doubleWidth = glyphMapItem_getOptions(mapItemPtr).doubleWidth;
  *mapItemPtr = GLYPHMAP_ITEM_MAKE(c, m_emuState.backgroundColor, m_emuState.foregroundColor, glyphOptions);

  if (glyphOptions.value != m_glyphOptions.value)
    m_canvas->setGlyphOptions(glyphOptions);

  int x = (m_emuState.cursorX - 1) * m_font.width * (glyphOptions.doubleWidth ? 2 : 1);
  int y = (m_emuState.cursorY - 1) * m_font.height;
  m_canvas->drawGlyph(x, y, m_font.width, m_font.height, m_font.data, c);

  if (glyphOptions.value != m_glyphOptions.value)
    m_canvas->setGlyphOptions(m_glyphOptions);

  // blinking text?
  if (m_glyphOptions.userOpt1)
    m_prevBlinkingTextEnabled = true; // consumeInputQueue() will set the value

  if (m_emuState.cursorX == m_columns) {
    m_emuState.cursorPastLastCol = true;
  } else {
    setCursorPos(m_emuState.cursorX + 1, m_emuState.cursorY);
  }

  return vscroll;
}


void Terminal::refresh()
{
  #if FABGLIB_TERMINAL_DEBUG_REPORT_DESCS
  log("refresh()\n");
  #endif

  refresh(1, 1, m_columns, m_rows);
}


// do not call waitCompletion!!
void Terminal::refresh(int X, int Y)
{
  #if FABGLIB_TERMINAL_DEBUG_REPORT_DESCS
  logFmt("refresh(%d, %d)\n", X, Y);
  #endif

  m_canvas->renderGlyphsBuffer(X - 1, Y - 1, &m_glyphsBuffer);
}


void Terminal::refresh(int X1, int Y1, int X2, int Y2)
{
  #if FABGLIB_TERMINAL_DEBUG_REPORT_DESCS
  logFmt("refresh(%d, %d, %d, %d)\n", X1, Y1, X2, Y2);
  #endif

  for (int y = Y1 - 1; y < Y2; ++y) {
    for (int x = X1 - 1; x < X2; ++x)
      m_canvas->renderGlyphsBuffer(x, y, &m_glyphsBuffer);
    m_canvas->waitCompletion(false);
  }
}


// value: 0 = normal, 1 = double width, 2 = double width - double height top, 3 = double width - double height bottom
void Terminal::setLineDoubleWidth(int row, int value)
{
  #if FABGLIB_TERMINAL_DEBUG_REPORT_DESCS
  logFmt("setLineDoubleWidth(%d, %d)\n", row, value);
  #endif

  uint32_t * mapItemPtr = m_glyphsBuffer.map + (row - 1) * m_columns;
  for (int i = 0; i < m_columns; ++i, ++mapItemPtr) {
    GlyphOptions glyphOptions = glyphMapItem_getOptions(mapItemPtr);
    glyphOptions.doubleWidth = value;
    glyphMapItem_setOptions(mapItemPtr, glyphOptions);
  }

  refresh(1, row, m_columns, row);
}


int Terminal::getCharWidthAt(int row)
{
  return glyphMapItem_getOptions(m_glyphsBuffer.map + (row - 1) * m_columns).doubleWidth ? m_font.width * 2 : m_font.width;
}


int Terminal::getColumnsAt(int row)
{
  return glyphMapItem_getOptions(m_glyphsBuffer.map + (row - 1) * m_columns).doubleWidth ? m_columns / 2 : m_columns;
}


GlyphOptions Terminal::getGlyphOptionsAt(int X, int Y)
{
  return glyphMapItem_getOptions(m_glyphsBuffer.map + (X - 1) + (Y - 1) * m_columns);
}


// blocking operation
char Terminal::getNextCode(bool processCtrlCodes)
{
  while (true) {
    char c;
    xQueueReceive(m_inputQueue, &c, portMAX_DELAY);

    if (m_uart)
      uartCheckInputQueueForFlowControl();

    // inside an ESC sequence we may find control characters!
    if (processCtrlCodes && ISCTRLCHAR(c))
      execCtrlCode(c);
    else
      return c;
  }
}


void Terminal::charsConsumerTask(void * pvParameters)
{
  Terminal * term = (Terminal*) pvParameters;

  while (true)
    term->consumeInputQueue();
}


void Terminal::consumeInputQueue()
{
  char c = getNextCode(false);  // blocking call. false: do not process ctrl chars

  xSemaphoreTake(m_mutex, portMAX_DELAY);

  m_prevCursorEnabled = int_enableCursor(false);
  m_prevBlinkingTextEnabled = enableBlinkingText(false);

  // ESC
  // Start escape sequence
  if (c == ASCII_ESC)
    consumeESC();

  else if (ISCTRLCHAR(c))
    execCtrlCode(c);

  else {
    if (m_emuState.characterSet[m_emuState.characterSetIndex] == 0 || (!m_emuState.ANSIMode && m_emuState.VT52GraphicsMode))
      c = DECGRAPH_TO_CP437[(uint8_t)c];
    setChar(c);
  }

  enableBlinkingText(m_prevBlinkingTextEnabled);
  int_enableCursor(m_prevCursorEnabled);

  xSemaphoreGive(m_mutex);

  if (m_resetRequested)
    reset();
}


void Terminal::execCtrlCode(char c)
{
  switch (c) {

    // BS
    // backspace, move cursor one position to the left (without wrap).
    case ASCII_BS:
      if (m_emuState.cursorX > 1)
        setCursorPos(m_emuState.cursorX - 1, m_emuState.cursorY);
      else if (m_emuState.reverseWraparoundMode) {
        int newX = m_columns;
        int newY = m_emuState.cursorY - 1;
        if (newY == 0)
          newY = m_rows;
        setCursorPos(newX, newY);
      }
      break;

    // HT
    // Go to next tabstop or end of line if no tab stop
    case ASCII_HT:
      nextTabStop();
      break;

    // LF
    // Line feed
    case ASCII_LF:
      if (!m_emuState.cursorPastLastCol) {
        if (m_emuState.newLineMode)
          setCursorPos(1, m_emuState.cursorY);
        if (moveDown())
          scrollUp();
      }
      break;

    // VT (vertical tab)
    // FF (form feed)
    // Move cursor down
    case ASCII_VT:
    case ASCII_FF:
      if (moveDown())
        scrollUp();
      break;

    // CR
    // Carriage return. Move cursor at the beginning of the line.
    case ASCII_CR:
      setCursorPos(1, m_emuState.cursorY);
      break;

    // SO
    // Shift Out. Switch to Alternate Character Set (G1)
    case ASCII_SO:
      m_emuState.characterSetIndex = 1;
      break;

    // SI
    // Shift In. Switch to Standard Character Set (G0)
    case ASCII_SI:
      m_emuState.characterSetIndex = 0;
      break;

    case ASCII_DEL:
      // nothing to do
      break;

    default:
      break;
  }
}


// consume non-CSI and CSI (ESC is already consumed)
void Terminal::consumeESC()
{

  if (!m_emuState.ANSIMode) {
    consumeESCVT52();
    return;
  }

  char c = getNextCode(true);   // true: process ctrl chars

  if (c == '[') {
    // ESC [ : start of CSI sequence
    consumeCSI();
    return;
  }

  if (c == 0xFF && m_emuState.allowFabGLSequences > 0) {
    // ESC 0xFF : FabGL specific sequence
    consumeFabGLSeq();
    return;
  }

  if (c == 'P') {
    // ESC P : start of DCS sequence
    consumeDCS();
    return;
  }

  #if FABGLIB_TERMINAL_DEBUG_REPORT_ESC
  logFmt("ESC%c\n", c);
  #endif

  switch (c) {

    // ESC c : RIS, reset terminal.
    case 'c':
      m_resetRequested = true;  // reset() actually called by consumeInputQueue()
      break;

    // ESC D : IND, line feed.
    case 'D':
      if (moveDown())
        scrollUp();
      break;

    // ESC E : NEL, new line.
    case 'E':
      setCursorPos(1, m_emuState.cursorY);
      if (moveDown())
        scrollUp();
      break;

    // ESC H : HTS, set tab stop at current column.
    case 'H':
      setTabStop(m_emuState.cursorX, true);
      break;

    // ESC M : RI, move up one line keeping column position.
    case 'M':
      if (moveUp())
        scrollDown();
      break;

    // ESC Z : DECID, returns TERMID
    case 'Z':
      //log("DECID\n");
      sendCSI();
      send(TERMID);
      break;

    // ESC 7 : DECSC, save current cursor state (position and attributes)
    case '7':
      saveCursorState();
      break;

    // ESC 8 : DECRC, restore current cursor state (position and attributes)
    case '8':
      restoreCursorState();
      break;

    // ESC #
    case '#':
      c = getNextCode(true);  // true: process ctrl chars
      switch (c) {
        // ESC # 3 : DECDHL, DEC double-height line, top half
        case '3':
          setLineDoubleWidth(m_emuState.cursorY, 2);
          break;
        // ESC # 4 : DECDHL, DEC double-height line, bottom half
        case '4':
          setLineDoubleWidth(m_emuState.cursorY, 3);
          break;
        // ESC # 5 : DECSWL, DEC single-width line
        case '5':
          setLineDoubleWidth(m_emuState.cursorY, 0);
          break;
        // ESC # 6 : DECDWL, DEC double-width line
        case '6':
          setLineDoubleWidth(m_emuState.cursorY, 1);
          break;
        // ESC # 8 :DECALN, DEC screen alignment test - fill screen with E's.
        case '8':
          erase(1, 1, m_columns, m_rows, 'E', false, false);
          break;
      }
      break;

    // Start sequence defining character set:
    // ESC character_set_index character_set
    // character_set_index: '(' = G0  ')' = G1   '*' = G2   '+' = G3
    // character_set: '0' = VT100 graphics mapping    '1' = VT100 graphics mapping    'B' = USASCII
    case '(':
    case ')':
    case '*':
    case '+':
      switch (getNextCode(true)) {
        case '0':
        case '2':
          m_emuState.characterSet[c - '('] = 0; // DEC Special Character and Line Drawing
          break;
        default:  // 'B' and others
          m_emuState.characterSet[c - '('] = 1; // United States (USASCII)
          break;
      }
      break;

    // ESC = : DECKPAM (Keypad Application Mode)
    case '=':
      m_emuState.keypadMode = KeypadMode::Application;
      #if FABGLIB_TERMINAL_DEBUG_REPORT_DESCSALL
      log("Keypad Application Mode\n");
      #endif
      break;

    // ESC > : DECKPNM (Keypad Numeric Mode)
    case '>':
      m_emuState.keypadMode = KeypadMode::Numeric;
      #if FABGLIB_TERMINAL_DEBUG_REPORT_DESCSALL
      log("Keypad Numeric Mode\n");
      #endif
      break;

    case ASCII_SPC:
      switch (getNextCode(true)) {

        // ESC SPC F : S7C1T, Select 7-Bit C1 Control Characters
        case 'F':
          m_emuState.ctrlBits = 7;
          break;

        // ESC SPC G : S8C1T, Select 8-Bit C1 Control Characters
        case 'G':
          if (m_emuState.conformanceLevel >= 2 && m_emuState.ANSIMode)
            m_emuState.ctrlBits = 8;
          break;
      }
      break;

    // consume unknow char
    default:
      #if FABGLIB_TERMINAL_DEBUG_REPORT_UNSUPPORT
      logFmt("Unknown ESC %c\n", c);
      #endif
      break;
  }
}


// a parameter is a number. Parameters are separated by ';'. Example: "5;27;3"
// first parameter has index 0
// params array must have up to FABGLIB_MAX_CSI_PARAMS
char Terminal::consumeParamsAndGetCode(int * params, int * paramsCount, bool * questionMarkFound)
{
  // get parameters until maximum size reached or a command character has been found
  *paramsCount = 1; // one parameter is always assumed (even if not exists)
  *questionMarkFound = false;
  int * p = params;
  *p = 0;
  while (true) {
    char c = getNextCode(true);  // true: process ctrl chars

    #if FABGLIB_TERMINAL_DEBUG_REPORT_ESC
    log(c);
    #endif

    if (c == '?') {
      *questionMarkFound = true;
      continue;
    }

    // break the loop if a command has been found
    if (!isdigit(c) && c != ';') {

      #if FABGLIB_TERMINAL_DEBUG_REPORT_ESC
      log('\n');
      #endif

      // reset non specified parameters
      while (p < params + FABGLIB_MAX_CSI_PARAMS)
        *(++p) = 0;

      return c;
    }

    if (p < params + FABGLIB_MAX_CSI_PARAMS) {
      if (c == ';') {
        ++p;
        *p = 0;
        ++(*paramsCount);
      } else {
        // this is a digit
        *p = *p * 10 + (c - '0');
      }
    }
  }
}


// consume CSI sequence (ESC + '[' already consumed)
void Terminal::consumeCSI()
{
  #if FABGLIB_TERMINAL_DEBUG_REPORT_ESC
  log("ESC[");
  #endif

  bool questionMarkFound;
  int params[FABGLIB_MAX_CSI_PARAMS];
  int paramsCount;
  char c = consumeParamsAndGetCode(params, &paramsCount, &questionMarkFound);

  // ESC [ ? ... h
  // ESC [ ? ... l
  if (questionMarkFound && (c == 'h' || c == 'l')) {
    consumeDECPrivateModes(params, paramsCount, c);
    return;
  }

  // ESC [ SPC ...
  if (c == ASCII_SPC) {
    consumeCSISPC(params, paramsCount);
    return;
  }

  // ESC [ " ...
  if (c == '"') {
    consumeCSIQUOT(params, paramsCount);
    return;
  }

  // process command in "c"
  switch (c) {

    // ESC [ H : CUP, Move cursor to the indicated row, column
    // ESC [ f : HVP, Move cursor to the indicated row, column
    case 'H':
    case 'f':
      setCursorPos(params[1], getAbsoluteRow(params[0]));
      break;

    // ESC [ g : TBC, Clear one or all tab stops
    case 'g':
      switch (params[0]) {
        case 0:
          setTabStop(m_emuState.cursorX, false); // clear tab stop at cursor
          break;
        case 3:
          setTabStop(0, false);         // clear all tab stops
          break;
      }
      break;

    // ESC [ C : CUF, Move cursor right the indicated # of columns.
    case 'C':
      setCursorPos(m_emuState.cursorX + tmax(1, params[0]), m_emuState.cursorY);
      break;

    // ESC [ P : DCH, Delete the indicated # of characters on current line.
    case 'P':
      deleteAt(m_emuState.cursorX, m_emuState.cursorY, tmax(1, params[0]));
      break;

    // ESC [ A : CUU, Move cursor up the indicated # of rows.
    case 'A':
      setCursorPos(m_emuState.cursorX, getAbsoluteRow(m_emuState.cursorY - tmax(1, params[0])));
      break;

    // ESC [ Ps J : ED, Erase display
    // ESC [ ? Ps J : DECSED, Selective Erase in Display
    // Ps = 0 : from cursor to end of display (default)
    // Ps = 1 : erase from start to cursor
    // Ps = 2 : erase whole display
    // Erase also doubleWidth attributes
    case 'J':
      switch (params[0]) {
        case 0:
          erase(m_emuState.cursorX, m_emuState.cursorY, m_columns, m_emuState.cursorY, ASCII_SPC, false, questionMarkFound);
          erase(1, m_emuState.cursorY + 1, m_columns, m_rows, ASCII_SPC, false, questionMarkFound);
          break;
        case 1:
          erase(1, 1, m_columns, m_emuState.cursorY - 1, ASCII_SPC, false, questionMarkFound);
          erase(1, m_emuState.cursorY, m_emuState.cursorX, m_emuState.cursorY, ASCII_SPC, false, questionMarkFound);
          break;
        case 2:
          erase(1, 1, m_columns, m_rows, ASCII_SPC, false, questionMarkFound);
          break;
      }
      break;

    // ESC [ Ps K :  EL, Erase line
    // ESC [ ? Ps K : DECSEL, Selective Erase in line
    // Ps = 0 : from cursor to end of line (default)
    // Ps = 1 : erase from start of line to cursor
    // Ps = 2 : erase whole line
    // Maintain doubleWidth attributes
    case 'K':
      switch (params[0]) {
        case 0:
          erase(m_emuState.cursorX, m_emuState.cursorY, m_columns, m_emuState.cursorY, ASCII_SPC, true, questionMarkFound);
          break;
        case 1:
          erase(1, m_emuState.cursorY, m_emuState.cursorX, m_emuState.cursorY, ASCII_SPC, true, questionMarkFound);
          break;
        case 2:
          erase(1, m_emuState.cursorY, m_columns, m_emuState.cursorY, ASCII_SPC, true, questionMarkFound);
          break;
      }
      break;

    // ESC [ Pn X : ECH, Erase Characters
    // Pn: number of characters to erase from cursor position (default is 1) up to the end of line
    case 'X':
      erase(m_emuState.cursorX, m_emuState.cursorY, tmin((int)m_columns, m_emuState.cursorX + tmax(1, params[0]) - 1), m_emuState.cursorY, ASCII_SPC, true, false);
      break;

    // ESC [ r : DECSTBM, Set scrolling region; parameters are top and bottom row.
    case 'r':
      setScrollingRegion(tmax(params[0], 1), (params[1] < 1 ? m_rows : params[1]));
      break;

    // ESC [ d : VPA, Move cursor to the indicated row, current column.
    case 'd':
      setCursorPos(m_emuState.cursorX, params[0]);
      break;

    // ESC [ G : CHA, Move cursor to indicated column in current row.
    case 'G':
      setCursorPos(params[0], m_emuState.cursorY);
      break;

    // ESC [ S : SU, Scroll up # lines (default = 1)
    case 'S':
      for (int i = tmax(1, params[0]); i > 0; --i)
        scrollUp();
      break;

    // ESC [ T : SD, Scroll down # lines (default = 1)
    case 'T':
      for (int i = tmax(1, params[0]); i > 0; --i)
        scrollDown();
      break;

    // ESC [ D : CUB, Cursor left
    case 'D':
    {
      int newX = m_emuState.cursorX - tmax(1, params[0]);
      if (m_emuState.reverseWraparoundMode && newX < 1) {
        newX = -newX;
        int newY = m_emuState.cursorY - newX / m_columns - 1;
        if (newY < 1)
          newY = m_rows + newY;
        newX = m_columns - (newX % m_columns);
        setCursorPos(newX, newY);
      } else
        setCursorPos(tmax(1, newX), m_emuState.cursorY);
      break;
    }

    // ESC [ B : CUD, Cursor down
    case 'B':
      setCursorPos(m_emuState.cursorX, getAbsoluteRow(m_emuState.cursorY + tmax(1, params[0])));
      break;

    // ESC [ m : SGR, Character Attributes
    case 'm':
      execSGRParameters(params, paramsCount);
      break;

    // ESC [ L : IL, Insert Lines starting at cursor (default 1 line)
    case 'L':
      for (int i = tmax(1, params[0]); i > 0; --i)
        scrollDownAt(m_emuState.cursorY);
      break;

    // ESC [ M : DL, Delete Lines starting at cursor (default 1 line)
    case 'M':
      for (int i = tmax(1, params[0]); i > 0; --i)
        scrollUpAt(m_emuState.cursorY);
      break;

    // ESC [ h : SM, Set Mode
    // ESC [ l : SM, Unset Mode
    case 'h':
    case 'l':
      switch (params[0]) {

        // IRM, Insert Mode
        case 4:
          m_emuState.insertMode = (c == 'h');
          break;

        // LNM, Automatic Newline
        case 20:
          m_emuState.newLineMode = (c == 'h');
          break;

        default:
          #if FABGLIB_TERMINAL_DEBUG_REPORT_UNSUPPORT
          logFmt("Unknown: ESC [ %d %c\n", params[0], c);
          #endif
          break;
      }
      break;

    // ESC [ @ : ICH, Insert Character (default 1 character)
    case '@':
      insertAt(m_emuState.cursorX, m_emuState.cursorY, tmax(1, params[0]));
      break;

    // ESC [ 0 c : Send Device Attributes
    case 'c':
      if (params[0] == 0) {
        sendCSI();
        send(TERMID);
      }
      break;

    // ESC [ Ps q : DECLL, Load LEDs
    case 'q':
      paramsCount = tmax(1, paramsCount);  // default paramater in case no params are provided
      for (int i = 0; i < paramsCount; ++i) {
        bool numLock, capsLock, scrollLock;
        m_keyboard->getLEDs(&numLock, &capsLock, &scrollLock);
        switch (params[i]) {
          case 0:
            numLock = capsLock = scrollLock = false;
            break;
          case 1:
            numLock = true;
            break;
          case 2:
            capsLock = true;
            break;
          case 3:
            scrollLock = true;
            break;
          case 21:
            numLock = false;
            break;
          case 22:
            capsLock = false;
            break;
          case 23:
            scrollLock = false;
            break;
        }
        m_keyboard->setLEDs(numLock, capsLock, scrollLock);
      }
      break;

    // ESC [ Ps n : DSR, Device Status Report
    case 'n':
      switch (params[0]) {
        // Status Report
        case 5:
          sendCSI();
          send("0n");
          break;
        // Report Cursor Position (CPR)
        case 6:
        {
          sendCSI();
          char s[4];
          send(itoa(m_emuState.originMode ? m_emuState.cursorY - m_emuState.scrollingRegionTop + 1 : m_emuState.cursorY, s, 10));
          send(';');
          send(itoa(m_emuState.cursorX, s, 10));
          send('R');
          break;
        }
      }
      break;

    default:
      #if FABGLIB_TERMINAL_DEBUG_REPORT_UNSUPPORT
      log("Unknown: ESC [ ");
      if (questionMarkFound)
        log("? ");
      for (int i = 0; i < paramsCount; ++i)
        logFmt("%d %c ", params[i], i < paramsCount - 1 ? ';' : c);
      log('\n');
      #endif
      break;
  }
}


// consume CSI " sequences
void Terminal::consumeCSIQUOT(int * params, int paramsCount)
{
  char c = getNextCode(true);  // true: process ctrl chars

  switch (c) {

    // ESC [ P1; P2 " p : DECSCL, Select Conformance Level
    case 'p':
      m_emuState.conformanceLevel = params[0] - 60;
      if (params[0] == 61 || (paramsCount == 2 && params[1] == 1))
        m_emuState.ctrlBits = 7;
      else
        m_emuState.ctrlBits = 8;
      break;

    // ESC [ Ps " q : DECSCA, Select character protection attribute
    case 'q':
      m_glyphOptions.userOpt2 = (params[0] == 1 ? 1 : 0);
      break;

  }
}


// consume CSI SPC sequences
void Terminal::consumeCSISPC(int * params, int paramsCount)
{
  char c = getNextCode(true);  // true: process ctrl chars

  switch (c) {

    // ESC [ Ps SPC q : DECSCUSR, Set Cursor Style
    // Ps: 0..1 blinking block, 2 steady block, 3 blinking underline, 4 steady underline, 5 blinking bar, 6 steady bar
    case 'q':
      m_emuState.cursorStyle = params[0];
      m_emuState.cursorBlinkingEnabled = (params[0] == 0) || (params[0] & 1);
      break;

    default:
      #if FABGLIB_TERMINAL_DEBUG_REPORT_UNSUPPORT
      log("Unknown: ESC [ ");
      for (int i = 0; i < paramsCount; ++i)
        logFmt("%d %c ", params[i], i < paramsCount - 1 ? ';' : ASCII_SPC);
      logFmt(" %c\n", c);
      #endif
      break;
  }
}


// consume DEC Private Mode (DECSET/DECRST) sequences
// ESC [ ? # h     <- set
// ESC [ ? # l     <- reset
// "c" can be "h" or "l"
void Terminal::consumeDECPrivateModes(int const * params, int paramsCount, char c)
{
  bool set = (c == 'h');
  switch (params[0]) {

    // ESC [ ? 1 h
    // ESC [ ? 1 l
    // DECCKM (default off): Cursor Keys Mode
    case 1:
      m_emuState.cursorKeysMode = set;
      break;

    // ESC [ ? 2 h
    // ESC [ ? 2 l
    // DECANM (default on): ANSI Mode (off = VT52 Mode)
    case 2:
      m_emuState.ANSIMode = set;
      break;

    // ESC [ ? 3 h
    // ESC [ ? 3 l
    // DECCOLM (default off): 132 Column Mode
    case 3:
      if (m_emuState.allow132ColumnMode) {
        set132ColumnMode(set);
        int_clear();
        setCursorPos(1, 1);
      }
      break;

    // ESC [ ? 4 h
    // ESC [ ? 4 l
    // DECSCLM (default off): Scrolling mode (jump or smooth)
    case 4:
      m_emuState.smoothScroll = set;
      break;


    // ESC [ ? 5 h
    // ESC [ ? 5 l
    // DECSCNM (default off): Reverse Video
    case 5:
      reverseVideo(set);
      break;

    // ESC [ ? 6 h
    // ESC [ ? 6 l
    // DECOM (default off): Origin mode
    case 6:
      m_emuState.originMode = set;
      if (set)
        setCursorPos(m_emuState.cursorX, m_emuState.scrollingRegionTop);
      break;

    // ESC [ ? 7 h
    // ESC [ ? 7 l
    // DECAWM (default on): Wraparound mode
    case 7:
      m_emuState.wraparound = set;
      break;

    // ESC [ ? 8 h
    // ESC [ ? 8 l
    // DECARM (default on): Autorepeat mode
    case 8:
      m_emuState.keyAutorepeat = set;
      break;

    // ESC [ ? 12 h
    // ESC [ ? 12 l
    // Start Blinking Cursor
    case 12:
      m_emuState.cursorBlinkingEnabled = set;
      break;

    // ESC [ ? 25 h
    // ESC [ ? 25 l
    // DECTECM (default on): Make cursor visible.
    case 25:
      m_prevCursorEnabled = set;  // consumeInputQueue() will set the value
      break;

    // ESC [ ? 40 h
    // ESC [ ? 40 l
    // Allow 80 -> 132 column mode (default off)
    case 40:
      m_emuState.allow132ColumnMode = set;
      break;

    // ESC [ ? 45 h
    // ESC [ ? 45 l
    // Reverse-wraparound mode (default off)
    case 45:
      m_emuState.reverseWraparoundMode = set;
      break;

    // ESC [ ? 47 h
    // ESC [ ? 47 l
    // ESC [ ? 1047 h
    // ESC [ ? 1047 l
    // Use Alternate Screen Buffer
    case 47:
    case 1047:
      useAlternateScreenBuffer(set);
      break;

    // ESC [ ? 77 h
    // ESC [ ? 77 l
    // DECBKM (default off): Backarrow key Mode
    case 67:
      m_emuState.backarrowKeyMode = set;
      break;

    // ESC [ ? 1048 h  : Save cursor as in DECSC
    // ESC [ ? 1048 l  : Restore cursor as in DECSC
    case 1048:
      if (set)
        saveCursorState();
      else
        restoreCursorState();
      break;

    // ESC [ ? 1049 h
    // ESC [ ? 1049 l
    // Save cursor as in DECSC and use Alternate Screen Buffer
    case 1049:
      if (set) {
        saveCursorState();
        useAlternateScreenBuffer(true);
      } else {
        useAlternateScreenBuffer(false);
        restoreCursorState();
      }
      break;

    // ESC [ ? 7999 h
    // ESC [ ? 7999 l
    // Allows enhanced FabGL sequences (default disabled)
    // This set is "incremental". This is actually disabled when the counter reach 0.
    case 7999:
      m_emuState.allowFabGLSequences += set ? 1 : -1;
      if (m_emuState.allowFabGLSequences < 0)
        m_emuState.allowFabGLSequences = 0;
      break;

    default:
      #if FABGLIB_TERMINAL_DEBUG_REPORT_UNSUPPORT
      logFmt("Unknown DECSET/DECRST: %d %c\n", params[0], c);
      #endif
      break;
  }
}


// exec SGR: Select Graphic Rendition
// ESC [ ...params... m
void Terminal::execSGRParameters(int const * params, int paramsCount)
{
  for (; paramsCount; ++params, --paramsCount) {
    switch (*params) {

      // Normal
      case 0:
        m_glyphOptions.bold             = 0;
        m_glyphOptions.reduceLuminosity = 0;  // faint
        m_glyphOptions.italic           = 0;
        m_glyphOptions.underline        = 0;
        m_glyphOptions.userOpt1         = 0;  // blink
        m_glyphOptions.blank            = 0;  // invisible
        m_glyphOptions.invert           = 0;  // inverse
        int_setForegroundColor(m_defaultForegroundColor);
        int_setBackgroundColor(m_defaultBackgroundColor);
        break;

      // Bold
      case 1:
        m_glyphOptions.bold = 1;
        break;

      // Faint (decreased intensity)
      case 2:
        m_glyphOptions.reduceLuminosity = 1;
        break;

      // Disable Bold and Faint
      case 22:
        m_glyphOptions.bold = m_glyphOptions.reduceLuminosity = 0;
        break;

      // Italic
      case 3:
        m_glyphOptions.italic = 1;
        break;

      // Disable Italic
      case 23:
        m_glyphOptions.italic = 0;
        break;

      // Underline
      case 4:
        m_glyphOptions.underline = 1;
        break;

      // Disable Underline
      case 24:
        m_glyphOptions.underline = 0;
        break;

      // Blink
      case 5:
        m_glyphOptions.userOpt1 = 1;
        break;

      // Disable Blink
      case 25:
        m_glyphOptions.userOpt1 = 0;
        break;

      // Inverse
      case 7:
        m_glyphOptions.invert = 1;
        break;

      // Disable Inverse
      case 27:
        m_glyphOptions.invert = 0;
        break;

      // Invisible
      case 8:
        m_glyphOptions.blank = 1;
        break;

      // Disable Invisible
      case 28:
        m_glyphOptions.blank = 0;
        break;

      // Set Foreground color
      case 30 ... 37:
        int_setForegroundColor( (Color) (*params - 30) );
        break;

      // Set Foreground color to Default
      case 39:
        int_setForegroundColor(m_defaultForegroundColor);
        break;

      // Set Background color
      case 40 ... 47:
        int_setBackgroundColor( (Color) (*params - 40) );
        break;

      // Set Background color to Default
      case 49:
        int_setBackgroundColor(m_defaultBackgroundColor);
        break;

      // Set Bright Foreground color
      case 90 ... 97:
        int_setForegroundColor( (Color) (8 + *params - 90) );
        break;

      // Set Bright Background color
      case 100 ... 107:
        int_setBackgroundColor( (Color) (8 + *params - 100) );
        break;

      default:
        #if FABGLIB_TERMINAL_DEBUG_REPORT_UNSUPPORT
        logFmt("Unknown: ESC [ %d m\n", *params);
        #endif
        break;

    }
  }
  m_canvas->setGlyphOptions(m_glyphOptions);
}


// "ESC P" (DCS) already consumed
// consume from parameters to ST (that is ESC "\")
void Terminal::consumeDCS()
{
  #if FABGLIB_TERMINAL_DEBUG_REPORT_ESC
  log("ESC P");
  #endif

  // get parameters
  bool questionMarkFound;
  int params[FABGLIB_MAX_CSI_PARAMS];
  int paramsCount;
  char c = consumeParamsAndGetCode(params, &paramsCount, &questionMarkFound);

  // get DCS content up to ST
  char content[FABGLIB_MAX_DCS_CONTENT];
  int contentLength = 0;
  content[contentLength++] = c;
  while (true) {
    char c = getNextCode(false);  // false: do notprocess ctrl chars, ESC needed here
    if (c == ASCII_ESC) {
      if (getNextCode(false) == '\\')
        break;  // ST found
      else {
        #if FABGLIB_TERMINAL_DEBUG_REPORT_UNSUPPORT
        log("DCS failed, expected ST\n");
        #endif
        return;  // fail
      }
    } else if (contentLength == FABGLIB_MAX_DCS_CONTENT) {
      #if FABGLIB_TERMINAL_DEBUG_REPORT_UNSUPPORT
      log("DCS failed, content too long\n");
      #endif
      return; // fail
    }
    content[contentLength++] = c;
  }

  // $q : DECRQSS, Request Selection or Setting
  if (m_emuState.conformanceLevel >= 3 && contentLength > 2 && content[0] == '$' && content[1] == 'q') {

    // "p : request DECSCL setting, reply with: DCS 1 $ r DECSCL " p ST
    //   where DECSCL is: 6 m_emuState.conformanceLevel ; bits " p
    //   where bits is 0 = 8 bits, 1 = 7 bits
    if (contentLength == 4 && content[2] == '\"' && content[3] == 'p') {
      sendDCS();
      send("1$r6");
      send('0' + m_emuState.conformanceLevel);
      send(';');
      send(m_emuState.ctrlBits == 7 ? '1' : '0');
      send("\"p\e\\");
      return; // processed
    }

  }

  #if FABGLIB_TERMINAL_DEBUG_REPORT_UNSUPPORT
  log("Unknown: ESC P ");
  for (int i = 0; i < paramsCount; ++i)
    logFmt("%d %c ", params[i], i < paramsCount - 1 ? ';' : ASCII_SPC);
  logFmt("%.*s ESC \\\n", contentLength, content);
  #endif
}


void Terminal::consumeESCVT52()
{
  char c = getNextCode(false);

  #if FABGLIB_TERMINAL_DEBUG_REPORT_ESC
  logFmt("ESC%c\n", c);
  #endif

  switch (c) {

    // ESC < : Exit VT52 mode, goes to VT100 mode
    case '<':
      m_emuState.ANSIMode = true;
      m_emuState.conformanceLevel = 1;
      break;

    // ESC A : Cursor Up
    case 'A':
      setCursorPos(m_emuState.cursorX, m_emuState.cursorY - 1);
      break;

    // ESC B : Cursor Down
    case 'B':
      setCursorPos(m_emuState.cursorX, m_emuState.cursorY + 1);
      break;

    // ESC C : Cursor Right
    case 'C':
      setCursorPos(m_emuState.cursorX + 1, m_emuState.cursorY);
      break;

    // ESC D : Cursor Left
    case 'D':
      setCursorPos(m_emuState.cursorX -1, m_emuState.cursorY);
      break;

    // ESC H : Cursor to Home Position
    case 'H':
      setCursorPos(1, 1);
      break;

    // ESC I : Reverse Line Feed
    case 'I':
      if (moveUp())
        scrollDown();
      break;

    // ESC J : Erase from cursor to end of screen
    case 'J':
      erase(m_emuState.cursorX, m_emuState.cursorY, m_columns, m_emuState.cursorY, ASCII_SPC, false, false);
      erase(1, m_emuState.cursorY + 1, m_columns, m_rows, ASCII_SPC, false, false);
      break;

    // ESC K : Erase from cursor to end of line
    case 'K':
      erase(m_emuState.cursorX, m_emuState.cursorY, m_columns, m_emuState.cursorY, ASCII_SPC, true, false);
      break;

    // ESC Y row col : Direct Cursor Addressing
    case 'Y':
    {
      int row = getNextCode(false) - 31;
      int col = getNextCode(false) - 31;
      setCursorPos(col, row);
      break;
    }

    // ESC Z : Identify
    case 'Z':
      send("\e/Z");
      break;

    // ESC = : Enter Alternate Keypad Mode
    case '=':
      m_emuState.keypadMode = KeypadMode::Application;
      #if FABGLIB_TERMINAL_DEBUG_REPORT_DESCSALL
      log("Enter Alternate Keypad Mode\n");
      #endif
      break;

    // ESC > : Exit Alternate Keypad Mode
    case '>':
      m_emuState.keypadMode = KeypadMode::Numeric;
      #if FABGLIB_TERMINAL_DEBUG_REPORT_DESCSALL
      log("Exit Alternate Keypad Mode\n");
      #endif
      break;

    // ESC F : Enter Graphics Mode
    case 'F':
      m_emuState.VT52GraphicsMode = true;
      break;

    // ESC G : Exit Graphics Mode
    case 'G':
      m_emuState.VT52GraphicsMode = false;
      break;

    // consume unknow char
    default:
      #if FABGLIB_TERMINAL_DEBUG_REPORT_UNSUPPORT
      logFmt("Unknown ESC %c\n", c);
      #endif
      break;
  }

}


// consume FabGL specific sequence (ESC 0xFF ....)
void Terminal::consumeFabGLSeq()
{
  #if FABGLIB_TERMINAL_DEBUG_REPORT_ESC
  log("ESC 0xFF");
  #endif

  char c = getNextCode(false);   // false: don't process ctrl chars

  // process command in "c"
  switch (c) {

    // Get cursor horizontal position (1 = leftmost pos)
    // Seq:
    //    ESC 0xFF FABGL_ENTERM_GETCURSORCOL
    // params:
    //    none
    // return:
    //    byte: 0xFE   (reply tag)
    //    byte: column
    case FABGL_ENTERM_GETCURSORCOL:
      send(0xFE);
      send(m_emuState.cursorX);
      break;

    // Get cursor vertical position (1 = topmost pos)
    // Seq:
    //    ESC 0xFF FABGL_ENTERM_GETCURSORROW
    // params:
    //    none
    // return:
    //    byte: 0xFE   (reply tag)
    //    byte: row
    case FABGL_ENTERM_GETCURSORROW:
      send(0xFE);
      send(m_emuState.cursorY);
      break;

    // Get cursor position
    // Seq:
    //    ESC 0xFF FABGL_ENTERM_GETCURSORPOS
    // params:
    //    none
    // return:
    //    byte: 0xFE   (reply tag)
    //    byte: column
    //    byte: row
    case FABGL_ENTERM_GETCURSORPOS:
      send(0xFE);
      send(m_emuState.cursorX);
      send(m_emuState.cursorY);
      break;

    // Set cursor position
    // Seq:
    //   ESC 0xFF FABGL_ENTERM_SETCURSORPOS COL ROW
    // params:
    //   COL (byte): column (1 = first column)
    //   ROW (byte): row (1 = first row)
    case FABGL_ENTERM_SETCURSORPOS:
    {
      uint8_t col = getNextCode(false);
      uint8_t row = getNextCode(false);
      setCursorPos(col, getAbsoluteRow(row));
      break;
    }

    // Insert a blank space at current position, moving next CHARSTOMOVE characters to the right (even on multiple lines).
    // Advances cursor by one position. Characters after CHARSTOMOVE length are overwritter.
    // Vertical scroll may occurs.
    // Seq:
    //   ESC 0xFF FABGL_ENTERM_INSERTSPACE CHARSTOMOVE_L CHARSTOMOVE_H
    // params:
    //   CHARSTOMOVE_L, CHARSTOMOVE_H (byte): number of chars to move to the right by one position
    // return:
    //    byte: 0xFE   (reply tag)
    //    byte: 0 = vertical scroll not occurred, 1 = vertical scroll occurred
    case FABGL_ENTERM_INSERTSPACE:
    {
      uint8_t charsToMove_L = getNextCode(false);
      uint8_t charsToMove_H = getNextCode(false);
      bool scroll = multilineInsertChar(charsToMove_L | charsToMove_H << 8);
      send(0xFE);
      send(scroll);
      break;
    }

    // Delete character at current position, moving next CHARSTOMOVE characters to the left (even on multiple lines).
    // Characters after CHARSTOMOVE are filled with spaces.
    // Seq:
    //   ESC 0xFF FABGL_ENTERM_DELETECHAR CHARSTOMOVE_L CHARSTOMOVE_H
    // params:
    //   CHARSTOMOVE_L, CHARSTOMOVE_H (byte): number of chars to move to the left by one position
    case FABGL_ENTERM_DELETECHAR:
    {
      uint8_t charsToMove_L = getNextCode(false);
      uint8_t charsToMove_H = getNextCode(false);
      multilineDeleteChar(charsToMove_L | charsToMove_H << 8);
      break;
    }

    // Move cursor at left, wrapping lines if necessary
    // Seq:
    //   ESC 0xFF FABGL_ENTERM_CURSORLEFT COUNT_L COUNT_H
    // params:
    //   COUNT_L, COUNT_H (byte): number of positions to move to the left
    case FABGL_ENTERM_CURSORLEFT:
    {
      uint8_t count_L = getNextCode(false);
      uint8_t count_H = getNextCode(false);
      move(-(count_L | count_H << 8));
      break;
    }

    // Move cursor at right, wrapping lines if necessary
    // Seq:
    //   ESC 0xFF FABGL_ENTERM_CURSORRIGHT COUNT
    // params:
    //   COUNT (byte): number of positions to move to the right
    case FABGL_ENTERM_CURSORRIGHT:
    {
      uint8_t count_L = getNextCode(false);
      uint8_t count_H = getNextCode(false);
      move(count_L | count_H << 8);
      break;
    }

    // Sets char CHAR at current position and advance one position. Scroll if necessary.
    // This do not interpret character as a special code, but just sets it.
    // Seq:
    //   ESC 0xFF FABGL_ENTERM_SETCHAR CHAR
    // params:
    //   CHAR (byte): character to set
    // return:
    //    byte: 0xFE   (reply tag)
    //    byte: 0 = vertical scroll not occurred, 1 = vertical scroll occurred
    case FABGL_ENTERM_SETCHAR:
    {
      bool scroll = setChar(getNextCode(false));
      send(0xFE);
      send(scroll);
      break;
    }

    // Sets a sequence of chars starting from current position and advancing the cursor for each character. Scroll if necessary.
    // This do not interpret character as a special code, but just sets it.
    // Seq:
    //   ESC 0xFF FABGL_ENTERM_SETCHARS COUNT_L COUNT_H ...chars...
    // params:
    //   COUNT_L, COUNT_H (byte): number of characters to sets
    //   ...chars... (bytes): the characters to sets
    // return:
    //    byte: 0xFE   (reply tag)
    //    byte: 0 = vertical scroll not occurred, >0 = number of vertical scrolls occurred
    case FABGL_ENTERM_SETCHARS:
    {
      uint8_t count_L = getNextCode(false);
      uint8_t count_H = getNextCode(false);
      int count = count_L | count_H << 8;
      int scrolls = 0;
      for (int i = 0; i < count; ++i)
        scrolls += setChar(getNextCode(false));
      send(0xFE);
      send(scrolls);
      break;
    }

    default:
      #if FABGLIB_TERMINAL_DEBUG_REPORT_UNSUPPORT
      logFmt("Unknown: ESC 0xFF %02x\n", c);
      #endif
      break;
  }
}



void Terminal::keyboardReaderTask(void * pvParameters)
{
  Terminal * term = (Terminal*) pvParameters;

  while (true) {

    bool keyDown;
    VirtualKey vk = term->m_keyboard->getNextVirtualKey(&keyDown);

    if (keyDown) {

      if (!term->m_emuState.keyAutorepeat && term->m_lastPressedKey == vk)
        continue; // don't repeat
      term->m_lastPressedKey = vk;

      xSemaphoreTake(term->m_mutex, portMAX_DELAY);

      if (term->m_termInfo == nullptr) {
        if (term->m_emuState.ANSIMode)
          term->ANSIDecodeVirtualKey(vk);
        else
          term->VT52DecodeVirtualKey(vk);
      } else
        term->TermDecodeVirtualKey(vk);

      xSemaphoreGive(term->m_mutex);

    } else {
      // !keyDown
      term->m_lastPressedKey = VK_NONE;
    }

  }
}


void Terminal::sendCursorKeyCode(char c)
{
  if (m_emuState.cursorKeysMode)
    sendSS3();
  else
    sendCSI();
  send(c);
}


void Terminal::sendKeypadCursorKeyCode(char applicationCode, const char * numericCode)
{
  if (m_emuState.keypadMode == KeypadMode::Application) {
    sendSS3();
    send(applicationCode);
  } else {
    sendCSI();
    send(numericCode);
  }
}


void Terminal::ANSIDecodeVirtualKey(VirtualKey vk)
{
  switch (vk) {

    // cursor keys

    case VK_UP:
      sendCursorKeyCode('A');
      break;

    case VK_DOWN:
      sendCursorKeyCode('B');
      break;

    case VK_RIGHT:
      sendCursorKeyCode('C');
      break;

    case VK_LEFT:
      sendCursorKeyCode('D');
      break;

    // cursor keys - on numeric keypad

    case VK_KP_UP:
      sendKeypadCursorKeyCode('x', "A");
      break;

    case VK_KP_DOWN:
      sendKeypadCursorKeyCode('r', "B");
      break;

    case VK_KP_RIGHT:
      sendKeypadCursorKeyCode('v', "C");
      break;

    case VK_KP_LEFT:
      sendKeypadCursorKeyCode('t', "D");
      break;

    // PageUp, PageDown, Insert, Home, Delete, End

    case VK_PAGEUP:
      sendCSI();
      send("5~");
      break;

    case VK_PAGEDOWN:
      sendCSI();
      send("6~");
      break;

    case VK_INSERT:
      sendCSI();
      send("2~");
      break;

    case VK_HOME:
      sendCSI();
      send("1~");
      break;

    case VK_DELETE:
      sendCSI();
      send("3~");
      break;

    case VK_END:
      sendCSI();
      send("4~");
      break;

    // PageUp, PageDown, Insert, Home, Delete, End - on numeric keypad

    case VK_KP_PAGEUP:
      sendKeypadCursorKeyCode('y', "5~");
      break;

    case VK_KP_PAGEDOWN:
      sendKeypadCursorKeyCode('s', "6~");
      break;

    case VK_KP_INSERT:
      sendKeypadCursorKeyCode('p', "2~");
      break;

    case VK_KP_HOME:
      sendKeypadCursorKeyCode('w', "1~");
      break;

    case VK_KP_DELETE:
      sendKeypadCursorKeyCode('n', "3~");
      break;

    case VK_KP_END:
      sendKeypadCursorKeyCode('q', "4~");
      break;

    // Backspace

    case VK_BACKSPACE:
      send(m_emuState.backarrowKeyMode ? ASCII_BS : ASCII_DEL);
      break;

    // Function keys

    case VK_F1:
      sendSS3();
      send('P');
      break;

    case VK_F2:
      sendSS3();
      send('Q');
      break;

    case VK_F3:
      sendSS3();
      send('R');
      break;

    case VK_F4:
      sendSS3();
      send('S');
      break;

    case VK_F5:
      sendCSI();
      send("15~");
      break;

    case VK_F6:
      sendCSI();
      send("17~");
      break;

    case VK_F7:
      sendCSI();
      send("18~");
      break;

    case VK_F8:
      sendCSI();
      send("19~");
      break;

    case VK_F9:
      sendCSI();
      send("20~");
      break;

    case VK_F10:
      sendCSI();
      send("21~");
      break;

    case VK_F11:
      sendCSI();
      send("23~");
      break;

    case VK_F12:
      sendCSI();
      send("24~");
      break;

    // Printable keys

    default:
    {
      int ascii = m_keyboard->virtualKeyToASCII(vk);
      switch (ascii) {

        // RETURN (CR)?
        case ASCII_CR:
          if (m_emuState.newLineMode)
            send("\r\n");  // send CR LF  (0x0D 0x0A)
          else
            send('\r');    // send only CR (0x0D)
          break;

        default:
          if (ascii > -1)
            send(ascii);
          break;
      }
      break;
    }

  }
}


void Terminal::VT52DecodeVirtualKey(VirtualKey vk)
{
  switch (vk) {

    // cursor keys

    case VK_UP:
      send("\eA");
      break;

    case VK_DOWN:
      send("\eB");
      break;

    case VK_RIGHT:
      send("\eC");
      break;

    case VK_LEFT:
      send("\eD");
      break;

    // numeric keypad

    case VK_KP_0:
    case VK_KP_INSERT:
      send(m_emuState.keypadMode == KeypadMode::Application ? "\e?p" : "0");
      break;

    case VK_KP_1:
    case VK_KP_END:
      send(m_emuState.keypadMode == KeypadMode::Application ? "\e?q" : "1");
      break;

    case VK_KP_2:
    case VK_KP_DOWN:
      send(m_emuState.keypadMode == KeypadMode::Application ? "\e?r" : "2");
      break;

    case VK_KP_3:
    case VK_KP_PAGEDOWN:
      send(m_emuState.keypadMode == KeypadMode::Application ? "\e?s" : "3");
      break;

    case VK_KP_4:
    case VK_KP_LEFT:
      send(m_emuState.keypadMode == KeypadMode::Application ? "\e?t" : "4");
      break;

    case VK_KP_5:
    case VK_KP_CENTER:
      send(m_emuState.keypadMode == KeypadMode::Application ? "\e?u" : "5");
      break;

    case VK_KP_6:
    case VK_KP_RIGHT:
      send(m_emuState.keypadMode == KeypadMode::Application ? "\e?v" : "6");
      break;

    case VK_KP_7:
    case VK_KP_HOME:
      send(m_emuState.keypadMode == KeypadMode::Application ? "\e?w" : "7");
      break;

    case VK_KP_8:
    case VK_KP_UP:
      send(m_emuState.keypadMode == KeypadMode::Application ? "\e?x" : "8");
      break;

    case VK_KP_9:
    case VK_KP_PAGEUP:
      send(m_emuState.keypadMode == KeypadMode::Application ? "\e?y" : "9");
      break;

    case VK_KP_PERIOD:
    case VK_KP_DELETE:
      send(m_emuState.keypadMode == KeypadMode::Application ? "\e?n" : ".");
      break;

    case VK_KP_ENTER:
      send(m_emuState.keypadMode == KeypadMode::Application ? "\e?M" : "\r");
      break;


    // Printable keys

    default:
    {
      int ascii = m_keyboard->virtualKeyToASCII(vk);
      if (ascii > -1)
        send(ascii);
      break;
    }

  }
}


void Terminal::TermDecodeVirtualKey(VirtualKey vk)
{
  for (auto item = m_termInfo->kbdCtrlSet; item->vk != VK_NONE; ++item) {
    if (item->vk == vk) {
      send(item->ANSICtrlCode);
      return;
    }
  }

  // default behavior
  int ascii = m_keyboard->virtualKeyToASCII(vk);
  if (ascii > -1)
    send(ascii);
}



////////////////////////////////////////////////////////////////////////////////////////////////////////////
////////////////////////////////////////////////////////////////////////////////////////////////////////////
// TerminalController


TerminalController::TerminalController(Terminal * terminal)
  : m_terminal(terminal)
{
}


TerminalController::~TerminalController()
{
}


void TerminalController::begin()
{
  // enable fabgl sequences
  m_terminal->write("\e[?7999h");
}


void TerminalController::end()
{
  // disable (if not enabled before) fabgl sequences
  m_terminal->write("\e[?7999l");
}


void TerminalController::setCursorPos(int col, int row)
{
  m_terminal->write(FABGL_ENTERM_CMD);
  m_terminal->write(FABGL_ENTERM_SETCURSORPOS);
  m_terminal->write(col);
  m_terminal->write(row);
}


void TerminalController::cursorLeft(int count)
{
  m_terminal->write(FABGL_ENTERM_CMD);
  m_terminal->write(FABGL_ENTERM_CURSORLEFT);
  m_terminal->write(count & 0xff);
  m_terminal->write(count >> 8);
}


void TerminalController::cursorRight(int count)
{
  m_terminal->write(FABGL_ENTERM_CMD);
  m_terminal->write(FABGL_ENTERM_CURSORRIGHT);
  m_terminal->write(count & 0xff);
  m_terminal->write(count >> 8);
}


void TerminalController::getCursorPos(int * col, int * row)
{
  m_terminal->write(FABGL_ENTERM_CMD);
  m_terminal->write(FABGL_ENTERM_GETCURSORPOS);
  m_terminal->waitFor(0xFE);
  *col = m_terminal->read(-1);
  *row = m_terminal->read(-1);
}


int TerminalController::getCursorCol()
{
  m_terminal->write(FABGL_ENTERM_CMD);
  m_terminal->write(FABGL_ENTERM_GETCURSORCOL);
  m_terminal->waitFor(0xFE);
  return m_terminal->read(-1);
}


int TerminalController::getCursorRow()
{
  m_terminal->write(FABGL_ENTERM_CMD);
  m_terminal->write(FABGL_ENTERM_GETCURSORROW);
  m_terminal->waitFor(0xFE);
  return m_terminal->read(-1);
}


bool TerminalController::multilineInsertChar(int charsToMove)
{
  m_terminal->write(FABGL_ENTERM_CMD);
  m_terminal->write(FABGL_ENTERM_INSERTSPACE);
  m_terminal->write(charsToMove & 0xff);
  m_terminal->write(charsToMove >> 8);
  m_terminal->waitFor(0xFE);
  return m_terminal->read(-1);
}


void TerminalController::multilineDeleteChar(int charsToMove)
{
  m_terminal->write(FABGL_ENTERM_CMD);
  m_terminal->write(FABGL_ENTERM_DELETECHAR);
  m_terminal->write(charsToMove & 0xff);
  m_terminal->write(charsToMove >> 8);
}


bool TerminalController::setChar(char c)
{
  m_terminal->write(FABGL_ENTERM_CMD);
  m_terminal->write(FABGL_ENTERM_SETCHAR);
  m_terminal->write(c);
  m_terminal->waitFor(0xFE);
  return m_terminal->read(-1);
}


int TerminalController::setChars(char const * buffer, int count)
{
  m_terminal->write(FABGL_ENTERM_CMD);
  m_terminal->write(FABGL_ENTERM_SETCHARS);
  m_terminal->write(count & 0xff);
  m_terminal->write(count >> 8);
  for (int i = 0; i < count; ++i, ++buffer)
    m_terminal->write(*buffer);
  m_terminal->waitFor(0xFE);
  return m_terminal->read(-1);
}



////////////////////////////////////////////////////////////////////////////////////////////////////////////
////////////////////////////////////////////////////////////////////////////////////////////////////////////
// LineEditor


LineEditor::LineEditor(Terminal * terminal)
  : m_terminal(terminal),
    m_termctrl(terminal),
    m_text(nullptr),
    m_textLength(0),
    m_allocated(0),
    m_state(-1),
    m_insertMode(true)
{
}


LineEditor::~LineEditor()
{
  free(m_text);
}


void LineEditor::setLength(int newLength)
{
  if (m_allocated < newLength) {
    int allocated = imax(m_allocated * 2, newLength);
    m_text = (char*) realloc(m_text, allocated + 1);
    memset(m_text + m_allocated, 0, allocated - m_allocated + 1);
    m_allocated = allocated;
  }
  m_textLength = newLength;
}


void LineEditor::setText(char const * text, bool moveCursor)
{
  setText(text, strlen(text), moveCursor);
}


void LineEditor::setText(char const * text, int length, bool moveCursor)
{
  setLength(length);
  memcpy(m_text, text, length);
  m_text[length] = 0;
  m_state = -1;
  m_inputPos = moveCursor ? length : 0;
}


void LineEditor::beginInput()
{
  m_termctrl.begin();
  m_homeCol = m_termctrl.getCursorCol();
  m_homeRow = m_termctrl.getCursorRow();
  if (m_text) {
    // m_inputPos already set by setText()
    m_homeRow -= m_termctrl.setChars(m_text, strlen(m_text));
    if (m_inputPos == 0)
      m_termctrl.setCursorPos(m_homeCol, m_homeRow);
  } else {
    m_inputPos = 0;
  }
  m_state = 0;
}


void LineEditor::endInput()
{
  m_termctrl.end();
  m_state = -1;
  if (m_text == nullptr) {
    m_text = (char*) malloc(1);
    m_text[0] = 0;
  }
}


char const * LineEditor::edit(int maxLength, int timeOutMS)
{

  // init?
  if (m_state == -1)
    beginInput();

  while (true) {

    int c = m_terminal->read(timeOutMS);

    // timeout?
    if (c < 0)
      return nullptr;

    if (m_state == 1) {

      // ESC mode

      switch (c) {

        // "ESC [" => switch to CSI mode
        case '[':
          m_state = 31;
          break;

        default:
          m_state = 0;
          break;

      }

    } else if (m_state >= 31) {

      // CSI mode

      switch (c) {

        // "ESC [ D" : cursor Left
        case 'D':
          if (m_inputPos > 0) {
            int count = 1;
            if (m_terminal->keyboard()->isVKDown(VK_LCTRL)) {
              // CTRL + Cursor Left => start of previous word
              while (m_inputPos - count > 0 && (m_text[m_inputPos - count] == ASCII_SPC || m_text[m_inputPos - count - 1] != ASCII_SPC))
                ++count;
            }
            m_termctrl.cursorLeft(count);
            m_inputPos -= count;
          }
          m_state = 0;
          break;

        // "ESC [ C" : cursor right
        case 'C':
          if (m_inputPos < m_textLength) {
            int count = 1;
            if (m_terminal->keyboard()->isVKDown(VK_LCTRL)) {
              // CTRL + Cursor Right => start of next word
              while (m_text[m_inputPos + count] && (m_text[m_inputPos + count] == ASCII_SPC || m_text[m_inputPos + count - 1] != ASCII_SPC))
                ++count;
            }
            m_termctrl.cursorRight(count);
            m_inputPos += count;
          }
          m_state = 0;
          break;

        // '1'...'6' : special chars (PageUp, Insert, Home...)
        case '1' ... '6':
          // requires ending '~'
          m_state = c;
          break;

        // '~'
        case '~':
          switch (m_state) {

            // Home
            case '1':
              m_termctrl.setCursorPos(m_homeCol, m_homeRow);
              m_inputPos = 0;
              break;

            // End
            case '4':
              m_termctrl.cursorRight(m_textLength - m_inputPos);
              m_inputPos = m_textLength;
              break;

            // Delete
            case '3':
              if (m_inputPos < m_textLength) {
                memmove(m_text + m_inputPos, m_text + m_inputPos + 1, m_textLength - m_inputPos);
                m_termctrl.multilineDeleteChar(m_textLength - m_inputPos - 1);
                --m_textLength;
              }
              break;

            // Insert
            case '2':
              m_insertMode = !m_insertMode;
              break;

          }
          m_state = 0;
          break;

        default:
          m_state = 0;
          break;

      }

    } else {

      // normal mode

      switch (c) {

        // ESC, switch to ESC mode
        case 0x1B:
          m_state = 1;
          break;

        // DEL, delete character at left
        case 0x7F:
          if (m_inputPos > 0) {
            m_termctrl.cursorLeft(1);
            m_termctrl.multilineDeleteChar(m_textLength - m_inputPos);
            memmove(m_text + m_inputPos - 1, m_text + m_inputPos, m_textLength - m_inputPos + 1);
            --m_inputPos;
            --m_textLength;
          }
          break;

        // CR, newline and return the inserted text
        case 0x0D:
          m_termctrl.cursorRight(m_textLength - m_inputPos);
          m_terminal->write("\r\n");
          endInput();
          return m_text;

        // insert printable chars
        case 32 ... 126:
        case 128 ... 255:
          // TODO: should we stop input when text length reach the full screen (minus home pos)?
          if (maxLength == 0 || m_inputPos < maxLength) {
            // update internal buffer
            if (m_insertMode || m_inputPos == m_textLength) {
              setLength(m_textLength + 1);
              memmove(m_text + m_inputPos + 1, m_text + m_inputPos, m_textLength - m_inputPos);
            }
            m_text[m_inputPos++] = c;
            // update terminal
            if (m_insertMode && m_inputPos < m_textLength) {
              if (m_termctrl.multilineInsertChar(m_textLength - m_inputPos))
                --m_homeRow;  // scrolled
            }
            if (m_termctrl.setChar(c))
              --m_homeRow;  // scrolled
          }
          break;

      }
    }

  }
}



} // end of namespace
