danjulio/gCore-featherwing/software/FabGL/examples/HX8357/SimpleTerminalOut/SimpleTerminalOut.ino

/*
  Created by Fabrizio Di Vittorio (fdivitto2013@gmail.com) - www.fabgl.com
  Copyright (c) 2019-2020 Fabrizio Di Vittorio.
  All rights reserved.

  This file is part of FabGL Library.

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
  You should have received a copy of the GNU General Public License
  along with FabGL.  If not, see <http://www.gnu.org/licenses/>.
 */

/*
 * Ported to gCore by Dan Julio
 *   Press and hold power button for > 2 second, then release to power off
 *   
 * TFT Display signals:
 *   SCK  => GPIO 5
 *   MOSI => GPIO 18
 *   CS   => GPIO 15
 *   D/C  => GPIO 33
 *   RESX => UNUSED
 */



#include "fabgl.h"

#include "vtanimations.h"



fabgl::HX8357DController DisplayController;
fabgl::Terminal          Terminal;


#define TFT_SCK    5
#define TFT_MOSI   18
#define TFT_CS     15
#define TFT_DC     33
#define TFT_RESET  GPIO_UNUSED
#define TFT_SPIBUS VSPI_HOST

#define TS_CS      32
#define SD_CS      14


void setup()
{
  gcore_begin();   // First to hold power

  // Disable unused SPI CS
  pinMode(TS_CS, OUTPUT);
  digitalWrite(TS_CS, HIGH);
  pinMode(SD_CS, OUTPUT);
  digitalWrite(SD_CS, HIGH);
  
  Serial.begin(115200); Serial.write("\nHello\n"); // DEBUG ONLY

  DisplayController.begin(TFT_SCK, TFT_MOSI, TFT_DC, TFT_RESET, TFT_CS, TFT_SPIBUS);
  DisplayController.setResolution(TFT_320x480);
  DisplayController.setOrientation(fabgl::TFTOrientation::Rotate270);

  Terminal.begin(&DisplayController);

  //Terminal.setLogStream(Serial);  // DEBUG ONLY

  Terminal.loadFont(&fabgl::FONT_6x10);

  Terminal.enableCursor(true);
}


void slowPrintf(const char * format, ...)
{
  va_list ap;
  va_start(ap, format);
  int size = vsnprintf(nullptr, 0, format, ap) + 1;
  if (size > 0) {
    char buf[size + 1];
    vsnprintf(buf, size, format, ap);
    for (int i = 0; i < size; ++i) {
      Terminal.write(buf[i]);
      delay(25);
    }
  }
  va_end(ap);
}


void demo1()
{
  Terminal.write("\e[40;32m"); // background: black, foreground: green
  Terminal.write("\e[2J");     // clear screen
  Terminal.write("\e[1;1H");   // move cursor to 1,1
  slowPrintf("* * * *  W E L C O M E   T O   F a b G L  * * * *\r\n");
  slowPrintf("2019-2020 by Fabrizio Di Vittorio - www.fabgl.com\r\n");
  slowPrintf("===============================================\r\n\n");
  slowPrintf("This is a VGA Controller, PS2 Mouse and Keyboard Controller, Graphics Library,  Game Engine and ANSI/VT Terminal for the ESP32\r\n\n");
  slowPrintf("Current settings\r\n");
  slowPrintf("Screen Size   : %d x %d\r\n", DisplayController.getScreenWidth(), DisplayController.getScreenHeight());
  slowPrintf("Terminal Size : %d x %d\r\n", Terminal.getColumns(), Terminal.getRows());
  slowPrintf("Free Memory   : %d bytes\r\n", heap_caps_get_free_size(MALLOC_CAP_8BIT));
  slowPrintf("Battery       : %1.2fv ", gcore_get_batt_voltage());
  if (gcore_get_charge_state() == 2) slowPrintf("CHARGING");
  slowPrintf("\r\n\n");
}

void demo2()
{
  Terminal.write("\e[40;32m"); // background: black, foreground: green
  slowPrintf("8 or 64 colors supported (depends by GPIOs used)\r\n");
  slowPrintf("ANSI colors:\r\n");
  // foregrounds
  Terminal.write("\e[31mRED\t"); delay(500);
  Terminal.write("\e[32mGREEN\t"); delay(500);
  Terminal.write("\e[33mYELLOW\t"); delay(500);
  Terminal.write("\e[34mBLUE\t"); delay(500);
  Terminal.write("\e[35mMAGENTA\t"); delay(500);
  Terminal.write("\e[36mCYAN\t"); delay(500);
  Terminal.write("\e[37mWHITE\r\n"); delay(500);
  Terminal.write("\e[90mHBLACK\t"); delay(500);
  Terminal.write("\e[91mHRED\t"); delay(500);
  Terminal.write("\e[92mHGREEN\t"); delay(500);
  Terminal.write("\e[93mHYELLOW\t"); delay(500);
  Terminal.write("\e[94mHBLUE\t"); delay(500);
  Terminal.write("\e[95mHMAGENTA\t"); delay(500);
  Terminal.write("\e[96mHCYAN\t"); delay(500);
  Terminal.write("\e[97mHWHITE\r\n"); delay(500);
  // backgrounds
  Terminal.write("\e[40mBLACK\t"); delay(500);
  Terminal.write("\e[41mRED\e[40m\t"); delay(500);
  Terminal.write("\e[42mGREEN\e[40m\t"); delay(500);
  Terminal.write("\e[43mYELLOW\e[40m\t"); delay(500);
  Terminal.write("\e[44mBLUE\e[40m\t"); delay(500);
  Terminal.write("\e[45mMAGENTA\e[40m\t"); delay(500);
  Terminal.write("\e[46mCYAN\e[40m\t"); delay(500);
  Terminal.write("\e[47mWHITE\e[40m\r\n"); delay(500);
  Terminal.write("\e[100mHBLACK\e[40m\t"); delay(500);
  Terminal.write("\e[101mHRED\e[40m\t"); delay(500);
  Terminal.write("\e[102mHGREEN\e[40m\t"); delay(500);
  Terminal.write("\e[103mHYELLOW\e[40m\t"); delay(500);
  Terminal.write("\e[104mHBLUE\e[40m\t"); delay(500);
  Terminal.write("\e[105mHMAGENTA\e[40m\t"); delay(500);
  Terminal.write("\e[106mHCYAN\e[40m\r\n"); delay(500);
}

void demo3()
{
  Terminal.write("\e[40;32m"); // background: black, foreground: green
  slowPrintf("\nSupported styles:\r\n");
  slowPrintf("\e[0mNormal\r\n");
  slowPrintf("\e[1mBold\e[0m\r\n");
  slowPrintf("\e[3mItalic\e[0m\r\n");
  slowPrintf("\e[4mUnderlined\e[0m\r\n");
  slowPrintf("\e[5mBlink\e[0m\r\n");
  slowPrintf("\e[7mInverse\e[0m\r\n");
  slowPrintf("\e[1;3mBoldItalic\e[0m\r\n");
  slowPrintf("\e[1;3;4mBoldItalicUnderlined\e[0m\r\n");
  slowPrintf("\e[1;3;4;5mBoldItalicUnderlinedBlinking\e[0m\r\n");
  slowPrintf("\e[1;3;4;5;7mBoldItalicUnderlinedBlinkingInverse\e[0m\r\n");
  slowPrintf("\e#6Double Width Line\r\n");
  slowPrintf("\e#6\e#3Double Height Line\r\n"); // top half
  slowPrintf("\e#6\e#4Double Height Line\r\n"); // bottom half
}

void demo4()
{
  Canvas cv(&DisplayController);
  Terminal.write("\e[40;32m"); // background: black, foreground: green
  slowPrintf("\nMixed text and graphics:\r\n");
  slowPrintf("Points...\r\n");
  for (int i = 0; i < 500; ++i) {
    cv.setPenColor(random(256), random(256), random(256));
    cv.setPixel(random(cv.getWidth()), random(cv.getHeight()));
    delay(15);
  }
  delay(500);
  slowPrintf("\e[40;32mLines...\r\n");
  for (int i = 0; i < 50; ++i) {
    cv.setPenColor(random(256), random(256), random(256));
    cv.drawLine(random(cv.getWidth()), random(cv.getHeight()), random(cv.getWidth()), random(cv.getHeight()));
    delay(50);
  }
  delay(500);
  slowPrintf("\e[40;32mRectangles...\r\n");
  for (int i = 0; i < 50; ++i) {
    cv.setPenColor(random(256), random(256), random(256));
    cv.drawRectangle(random(cv.getWidth()), random(cv.getHeight()), random(cv.getWidth()), random(cv.getHeight()));
    delay(50);
  }
  delay(500);
  slowPrintf("\e[40;32mEllipses...\r\n");
  for (int i = 0; i < 50; ++i) {
    cv.setPenColor(random(256), random(256), random(256));
    cv.drawEllipse(random(cv.getWidth()), random(cv.getHeight()), random(cv.getWidth()), random(cv.getHeight()));
    delay(50);
  }
  for (int i = 0; i < 30; ++i) {
    Terminal.write("\e[40;32mScrolling...\r\n");
    delay(250);
  }
}

void demo5()
{
  Terminal.write("\e[40;93m"); // background: black, foreground: yellow
  Terminal.write("\e[2J");     // clear screen
  slowPrintf("\e[1;37HVT/ANSI animation");
  Terminal.write("\e[20h"); // automatic new line on
  Terminal.write("\e[92m"); // light-green
  Terminal.enableCursor(false);
  for (int j = 0; j < 4; ++j) {
    for (int i = 0; i < sizeof(vt_animation); ++i) {
      Terminal.write(vt_animation[i]);
      if (vt_animation[i] == 0x1B && vt_animation[i + 1] == 0x5B && vt_animation[i + 2] == 0x48)
        delay(120); // pause 100ms every frame
    }
  }
  Terminal.enableCursor(true);
  Terminal.write("\e[20l"); // automatic new line off
}

void loop()
{
  delay(1000);
  demo1();
  delay(4000);
  demo2();
  delay(4000);
  demo3();
  delay(4000);
  demo4();
  delay(4000);
  demo5();
  delay(4000);
}
